mjrgh/PinscapePico/ExpansionBoards/DIY-Friendly/MainBoard/deprecated/README.md

# Older Versions

This folder contains older versions of the board that are no longer
maintained.
