mjrgh/PinscapePico/OpenPinballDevice/Aliasing.png

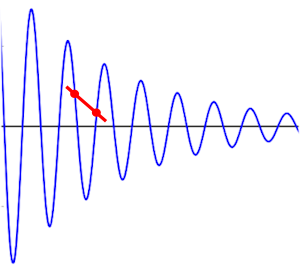
OpenPinballDevice/Aliasing.png
