mjrgh/PinscapePico/OpenPinballDevice/flipper-buttons-2.png

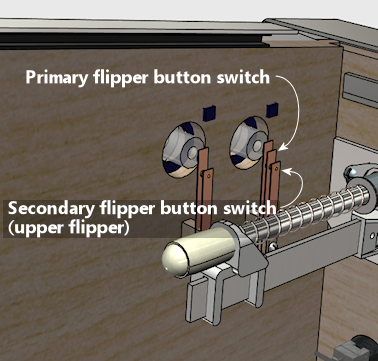
OpenPinballDevice/flipper-buttons-2.png
