mjrgh/PinscapePico/OpenPinballDevice/flipper-buttons.png

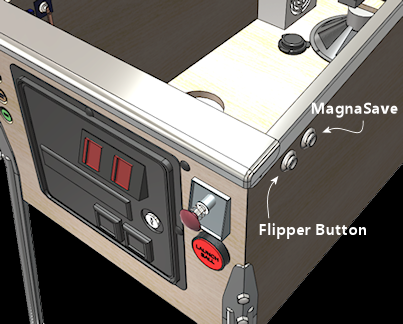
OpenPinballDevice/flipper-buttons.png
