mjrgh/PinscapePico/PWMWorker/DataSheet/high-side-led.png

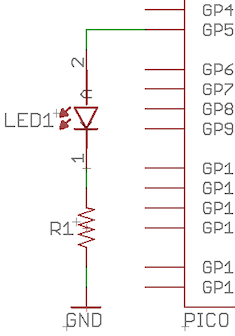
PWMWorker/DataSheet/high-side-led.png
