mjrgh/PinscapePico/PWMWorker/DataSheet/low-side-led.png

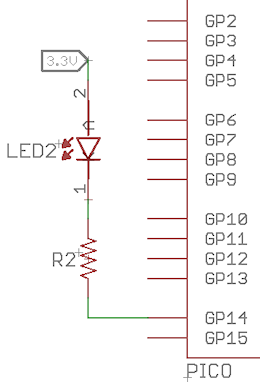
PWMWorker/DataSheet/low-side-led.png
