mjrgh/PinscapePico/PWMWorker/DataSheet/low-side-npn.png

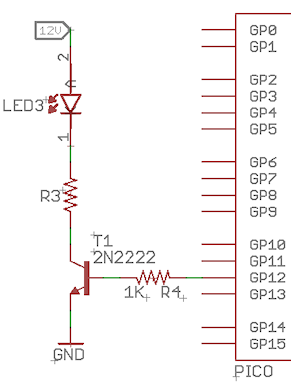
PWMWorker/DataSheet/low-side-npn.png
