mjrgh/PinscapePico/PWMWorker/DataSheet/mosfet-out.png

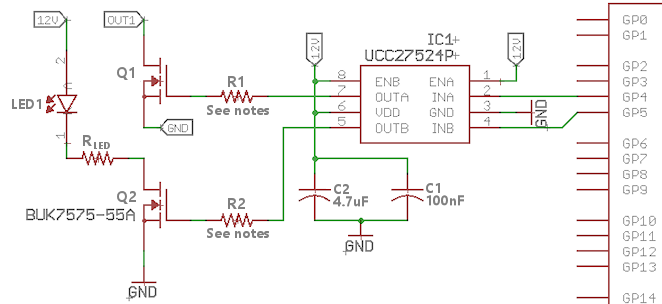
PWMWorker/DataSheet/mosfet-out.png
