mjrgh/PinscapePico/PWMWorker/DataSheet/PinMap.png

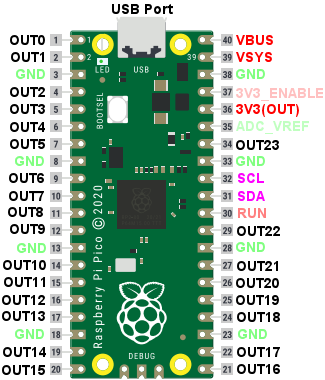
PWMWorker/DataSheet/PinMap.png
