mjrgh/PinscapePico/PWMWorker/DataSheet/PWM-graph.png

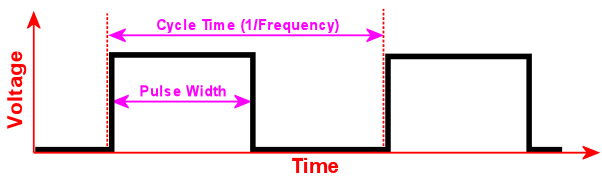
PWMWorker/DataSheet/PWM-graph.png
