mjrgh/PinscapePico/PWMWorker/DataSheet/uln2803.png

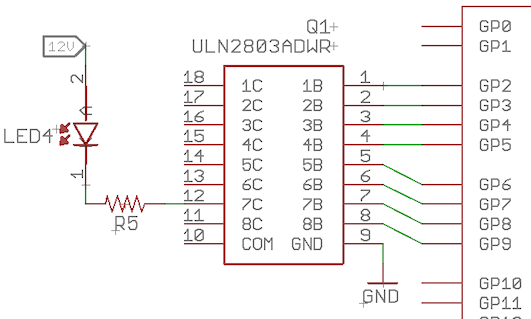
PWMWorker/DataSheet/uln2803.png
