mjrgh/PinscapePico/ScreenShots/ConfigToolButtons.png

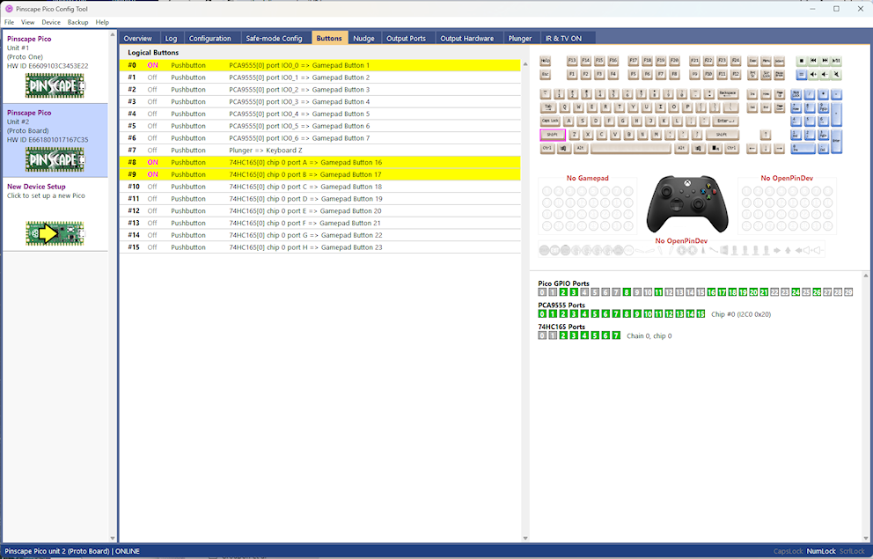
ScreenShots/ConfigToolButtons.png
