mjrgh/PinscapePico/ScreenShots/ConfigToolPlunger-thumb.png

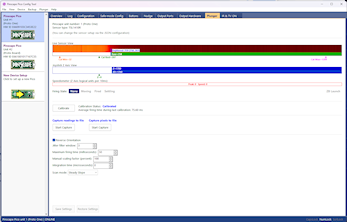
ScreenShots/ConfigToolPlunger-thumb.png
