mjrgh/PinscapePico/ExpansionBoards/KL25Z-Adapter/PinscapePico KL25Z Adapter - PCA9555 vsn.brd

## EAGLE design ExpansionBoards/KL25Z-Adapter/PinscapePico KL25Z Adapter - PCA9555 vsn.brd (2025-02-02)

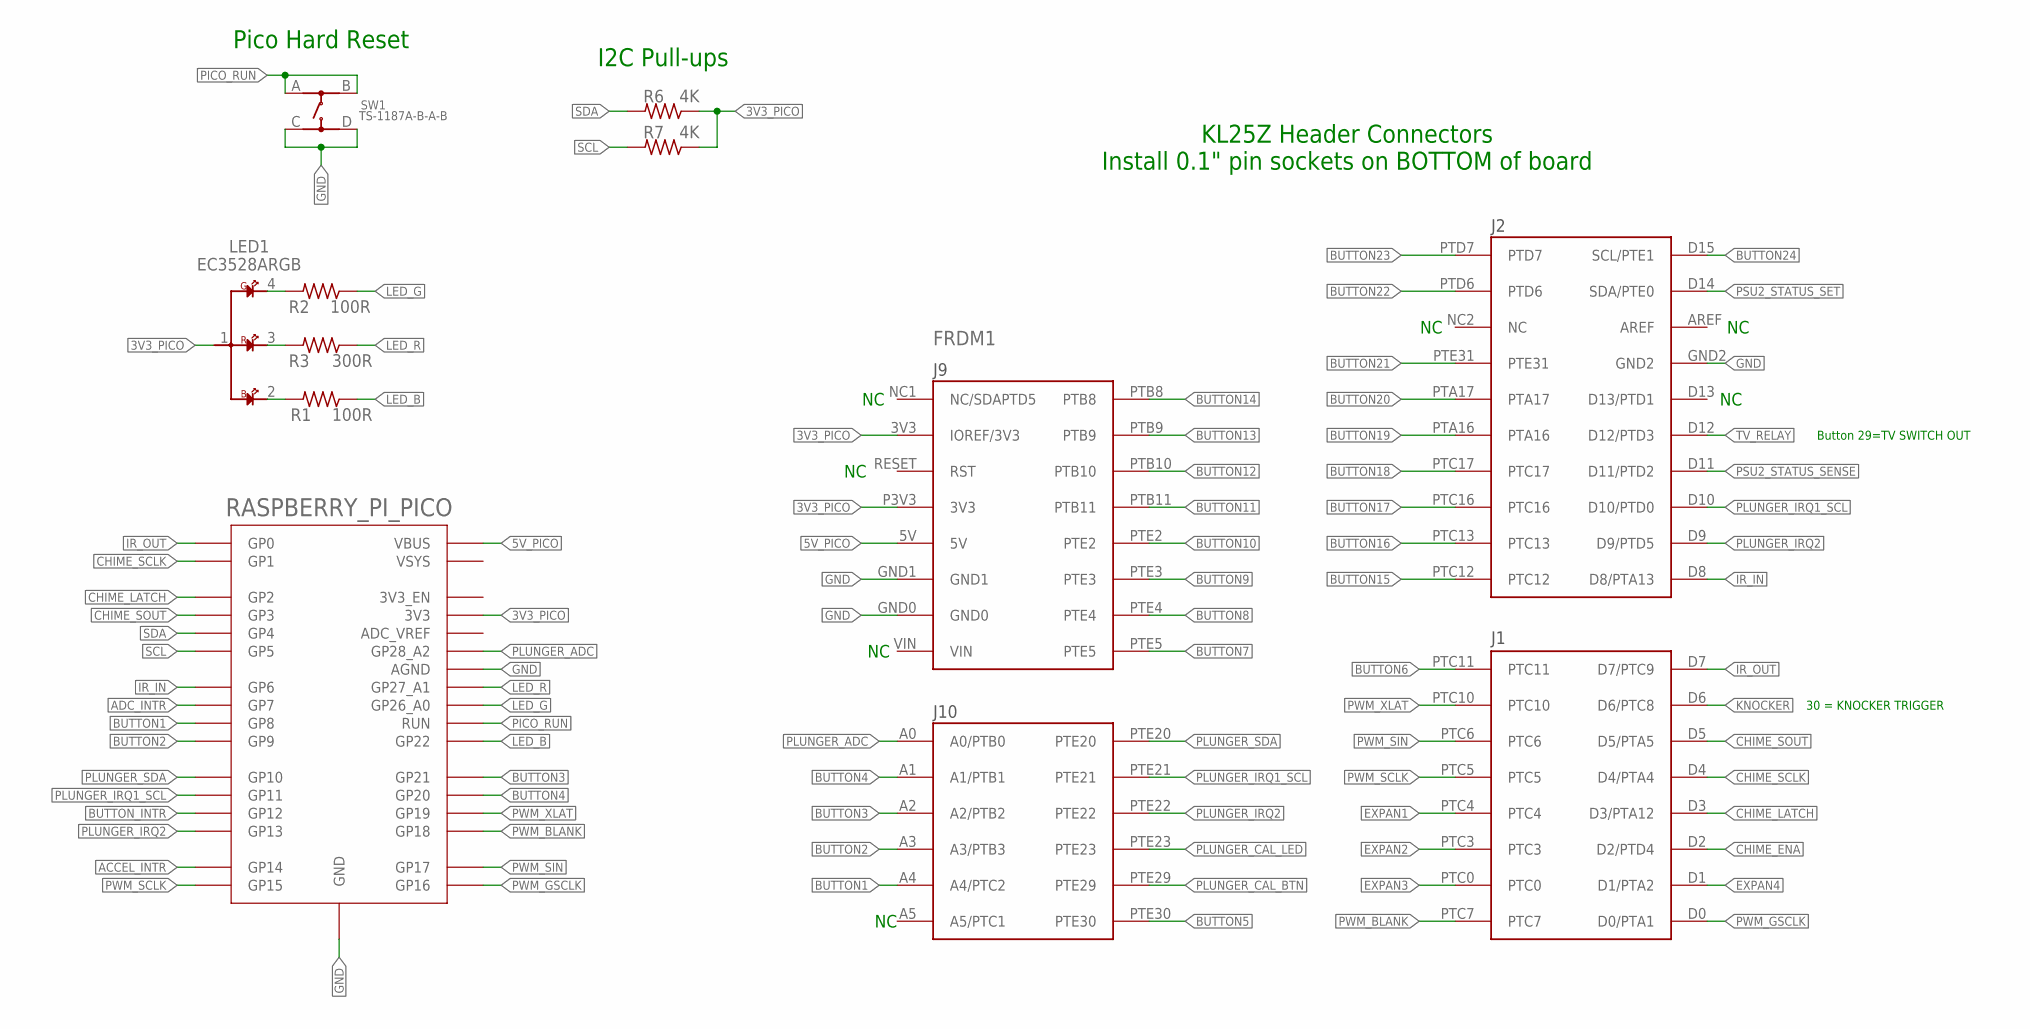
[picture p93: schematic PinscapePico KL25Z Adapter - PCA9555 vsn.sch, sheet 1, Main]

Parts:
FRDM1: KL25Z; FRDM_KL25Z_NORMAL
LED1: EC3528ARGB
R1, R2: 100R; R1206
R3: 300R; R1206
R6, R7: 4K; R1206
RASPBERRY_PI_PICO: RPI_PICO_NO_DEBUG; RPI_PICO_TH_NO_DEBUG
SW1: TS-1187A-B-A-B

Connections:
3V3_PICO: FRDM1.3V3 (IOREF/3V3), FRDM1.P3V3 (3V3), LED1.1, R6.1, R7.1, RASPBERRY_PI_PICO.3V3; also elsewhere on the board
5V_PICO: FRDM1.5V, RASPBERRY_PI_PICO.VBUS
ACCEL_INTR: RASPBERRY_PI_PICO.GP14; also elsewhere on the board
ADC_INTR: RASPBERRY_PI_PICO.GP7; also elsewhere on the board
BUTTON1: FRDM1.A4 (A4/PTC2), RASPBERRY_PI_PICO.GP8
BUTTON2: FRDM1.A3 (A3/PTB3), RASPBERRY_PI_PICO.GP9
BUTTON3: FRDM1.A2 (A2/PTB2), RASPBERRY_PI_PICO.GP21
BUTTON4: FRDM1.A1 (A1/PTB1), RASPBERRY_PI_PICO.GP20
BUTTON5: FRDM1.PTE30; also elsewhere on the board
BUTTON6: FRDM1.PTC11; also elsewhere on the board
BUTTON7: FRDM1.PTE5; also elsewhere on the board
BUTTON8: FRDM1.PTE4; also elsewhere on the board
BUTTON9: FRDM1.PTE3; also elsewhere on the board
BUTTON10: FRDM1.PTE2; also elsewhere on the board
BUTTON11: FRDM1.PTB11; also elsewhere on the board
BUTTON12: FRDM1.PTB10; also elsewhere on the board
BUTTON13: FRDM1.PTB9; also elsewhere on the board
BUTTON14: FRDM1.PTB8; also elsewhere on the board
BUTTON15: FRDM1.PTC12; also elsewhere on the board
BUTTON16: FRDM1.PTC13; also elsewhere on the board
BUTTON17: FRDM1.PTC16; also elsewhere on the board
BUTTON18: FRDM1.PTC17; also elsewhere on the board
BUTTON19: FRDM1.PTA16; also elsewhere on the board
BUTTON20: FRDM1.PTA17; also elsewhere on the board
BUTTON21: FRDM1.PTE31; also elsewhere on the board
BUTTON22: FRDM1.PTD6; also elsewhere on the board
BUTTON23: FRDM1.PTD7; also elsewhere on the board
BUTTON24: FRDM1.D15 (SCL/PTE1); also elsewhere on the board
BUTTON_INTR: RASPBERRY_PI_PICO.GP12; also elsewhere on the board
CHIME_ENA: FRDM1.D2 (D2/PTD4); also elsewhere on the board
CHIME_LATCH: FRDM1.D3 (D3/PTA12), RASPBERRY_PI_PICO.GP2
CHIME_SCLK: FRDM1.D4 (D4/PTA4), RASPBERRY_PI_PICO.GP1
CHIME_SOUT: FRDM1.D5 (D5/PTA5), RASPBERRY_PI_PICO.GP3
EXPAN1: FRDM1.PTC4; also elsewhere on the board
EXPAN2: FRDM1.PTC3; also elsewhere on the board
EXPAN3: FRDM1.PTC0; also elsewhere on the board
EXPAN4: FRDM1.D1 (D1/PTA2); also elsewhere on the board
GND: FRDM1.GND0, FRDM1.GND1, FRDM1.GND2, RASPBERRY_PI_PICO.AGND, RASPBERRY_PI_PICO.GND@1 (GND), RASPBERRY_PI_PICO.GND@2 (GND), RASPBERRY_PI_PICO.GND@3 (GND), RASPBERRY_PI_PICO.GND@4 (GND), RASPBERRY_PI_PICO.GND@6 (GND), RASPBERRY_PI_PICO.GND@7 (GND), RASPBERRY_PI_PICO.GND@8 (GND), SW1.C, SW1.D; also elsewhere on the board
IR_IN: FRDM1.D8 (D8/PTA13), RASPBERRY_PI_PICO.GP6
IR_OUT: FRDM1.D7 (D7/PTC9), RASPBERRY_PI_PICO.GP0
KNOCKER: FRDM1.D6 (D6/PTC8); also elsewhere on the board
LED_B: R1.1, RASPBERRY_PI_PICO.GP22
LED_G: R2.1, RASPBERRY_PI_PICO.GP26_A0
LED_R: R3.1, RASPBERRY_PI_PICO.GP27_A1
unnamed: LED1.3, R3.2
unnamed: LED1.2, R1.2
unnamed: LED1.4, R2.2
PICO_RUN: RASPBERRY_PI_PICO.RUN, SW1.A, SW1.B
PLUNGER_ADC: FRDM1.A0 (A0/PTB0), RASPBERRY_PI_PICO.GP28_A2; also elsewhere on the board
PLUNGER_CAL_BTN: FRDM1.PTE29; also elsewhere on the board
PLUNGER_CAL_LED: FRDM1.PTE23; also elsewhere on the board
PLUNGER_IRQ1_SCL: FRDM1.D10 (D10/PTD0), FRDM1.PTE21, RASPBERRY_PI_PICO.GP11
PLUNGER_IRQ2: FRDM1.D9 (D9/PTD5), FRDM1.PTE22, RASPBERRY_PI_PICO.GP13
PLUNGER_SDA: FRDM1.PTE20, RASPBERRY_PI_PICO.GP10
PSU2_STATUS_SENSE: FRDM1.D11 (D11/PTD2); also elsewhere on the board
PSU2_STATUS_SET: FRDM1.D14 (SDA/PTE0); also elsewhere on the board
PWM_BLANK: FRDM1.PTC7, RASPBERRY_PI_PICO.GP18
PWM_GSCLK: FRDM1.D0 (D0/PTA1), RASPBERRY_PI_PICO.GP16
PWM_SCLK: FRDM1.PTC5, RASPBERRY_PI_PICO.GP15
PWM_SIN: FRDM1.PTC6, RASPBERRY_PI_PICO.GP17
PWM_XLAT: FRDM1.PTC10, RASPBERRY_PI_PICO.GP19
SCL: R7.2, RASPBERRY_PI_PICO.GP5; also elsewhere on the board
SDA: R6.2, RASPBERRY_PI_PICO.GP4; also elsewhere on the board
TV_RELAY: FRDM1.D12 (D12/PTD3); also elsewhere on the board

Notes on the sheet:
Button 29=TV SWITCH OUT
30 = KNOCKER TRIGGER
Pico Hard Reset
I2C Pull-ups
KL25Z Header Connectors Install 0.1" pin sockets on BOTTOM of board

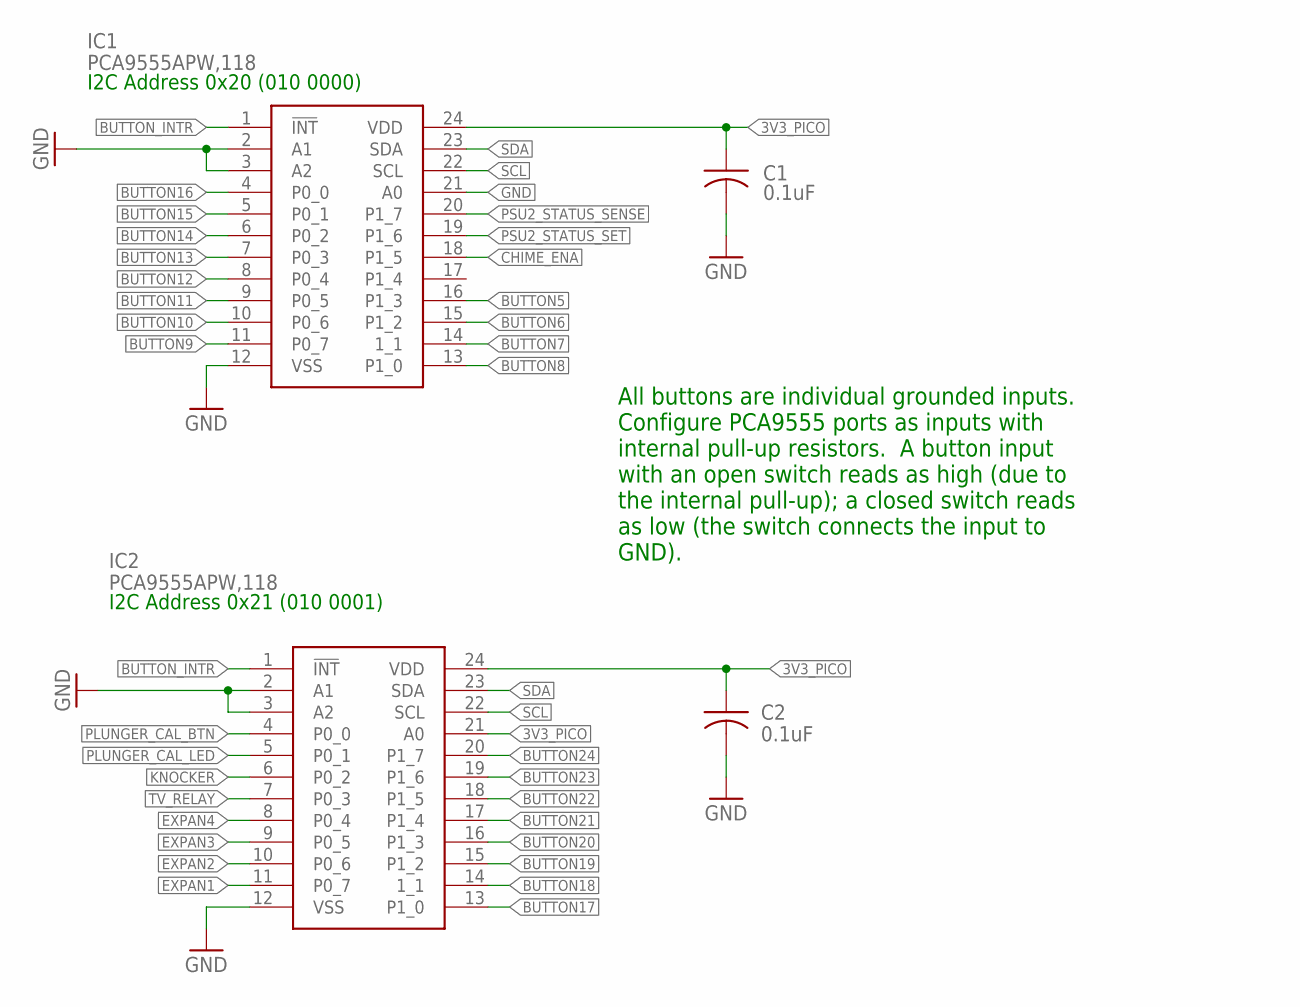
[picture p94: schematic PinscapePico KL25Z Adapter - PCA9555 vsn.sch, sheet 2, Buttons]

Parts:
C1, C2: 0.1uF; C1206
IC1, IC2: PCA9555APW,118; SOP65P640X110-24N

Connections:
3V3_PICO: C1.1, C2.1, IC1.24 (VDD), IC2.21 (A0), IC2.24 (VDD); also elsewhere on the board
BUTTON5: IC1.16 (P1_3); also elsewhere on the board
BUTTON6: IC1.15 (P1_2); also elsewhere on the board
BUTTON7: IC1.14 (1_1); also elsewhere on the board
BUTTON8: IC1.13 (P1_0); also elsewhere on the board
BUTTON9: IC1.11 (P0_7); also elsewhere on the board
BUTTON10: IC1.10 (P0_6); also elsewhere on the board
BUTTON11: IC1.9 (P0_5); also elsewhere on the board
BUTTON12: IC1.8 (P0_4); also elsewhere on the board
BUTTON13: IC1.7 (P0_3); also elsewhere on the board
BUTTON14: IC1.6 (P0_2); also elsewhere on the board
BUTTON15: IC1.5 (P0_1); also elsewhere on the board
BUTTON16: IC1.4 (P0_0); also elsewhere on the board
BUTTON17: IC2.13 (P1_0); also elsewhere on the board
BUTTON18: IC2.14 (1_1); also elsewhere on the board
BUTTON19: IC2.15 (P1_2); also elsewhere on the board
BUTTON20: IC2.16 (P1_3); also elsewhere on the board
BUTTON21: IC2.17 (P1_4); also elsewhere on the board
BUTTON22: IC2.18 (P1_5); also elsewhere on the board
BUTTON23: IC2.19 (P1_6); also elsewhere on the board
BUTTON24: IC2.20 (P1_7); also elsewhere on the board
BUTTON_INTR: IC1.1 (!INT), IC2.1 (!INT); also elsewhere on the board
CHIME_ENA: IC1.18 (P1_5); also elsewhere on the board
EXPAN1: IC2.11 (P0_7); also elsewhere on the board
EXPAN2: IC2.10 (P0_6); also elsewhere on the board
EXPAN3: IC2.9 (P0_5); also elsewhere on the board
EXPAN4: IC2.8 (P0_4); also elsewhere on the board
GND: C1.2, C2.2, IC1.2 (A1), IC1.3 (A2), IC1.12 (VSS), IC1.21 (A0), IC2.2 (A1), IC2.3 (A2), IC2.12 (VSS); also elsewhere on the board
KNOCKER: IC2.6 (P0_2); also elsewhere on the board
PLUNGER_CAL_BTN: IC2.4 (P0_0); also elsewhere on the board
PLUNGER_CAL_LED: IC2.5 (P0_1); also elsewhere on the board
PSU2_STATUS_SENSE: IC1.20 (P1_7); also elsewhere on the board
PSU2_STATUS_SET: IC1.19 (P1_6); also elsewhere on the board
SCL: IC1.22 (SCL), IC2.22 (SCL); also elsewhere on the board
SDA: IC1.23 (SDA), IC2.23 (SDA); also elsewhere on the board
TV_RELAY: IC2.7 (P0_3); also elsewhere on the board

Notes on the sheet:
I2C Address 0x20 (010 0000)
I2C Address 0x21 (010 0001)
All buttons are individual grounded inputs. Configure PCA9555 ports as inputs with internal pull-up resistors. A button input with an open switch reads as high (due to the internal pull-up); a closed switch reads as low (the switch connects the input to GND).

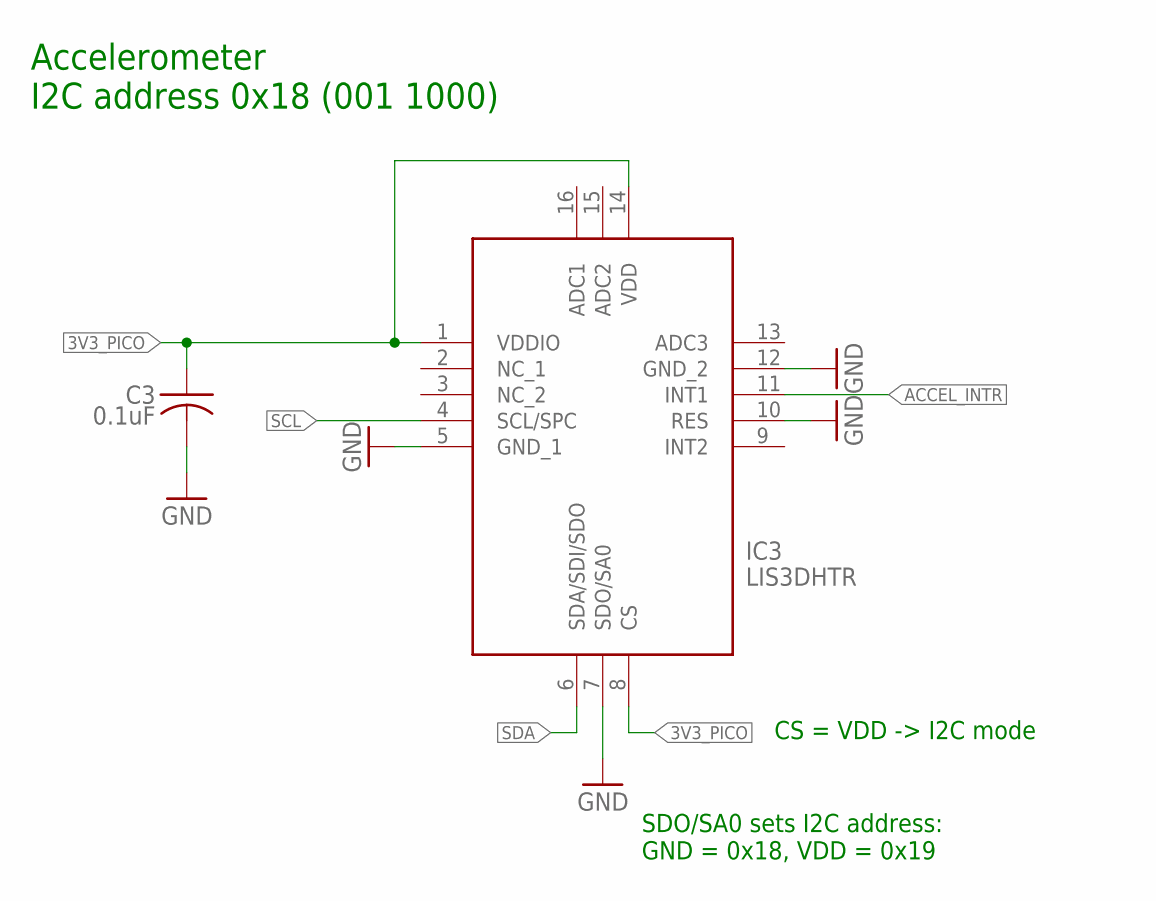
[picture p95: schematic PinscapePico KL25Z Adapter - PCA9555 vsn.sch, sheet 3, Accelerometer]

Parts:
C3: 0.1uF; C1206
IC3: LIS3DHTR

Connections:
3V3_PICO: C3.1, IC3.1 (VDDIO), IC3.8 (CS), IC3.14 (VDD); also elsewhere on the board
ACCEL_INTR: IC3.11 (INT1); also elsewhere on the board
GND: C3.2, IC3.5 (GND_1), IC3.7 (SDO/SA0), IC3.10 (RES), IC3.12 (GND_2); also elsewhere on the board
SCL: IC3.4 (SCL/SPC); also elsewhere on the board
SDA: IC3.6 (SDA/SDI/SDO); also elsewhere on the board

Notes on the sheet:
Accelerometer I2C address 0x18 (001 1000)
SDO/SA0 sets I2C address: GND = 0x18, VDD = 0x19
CS = VDD -> I2C mode

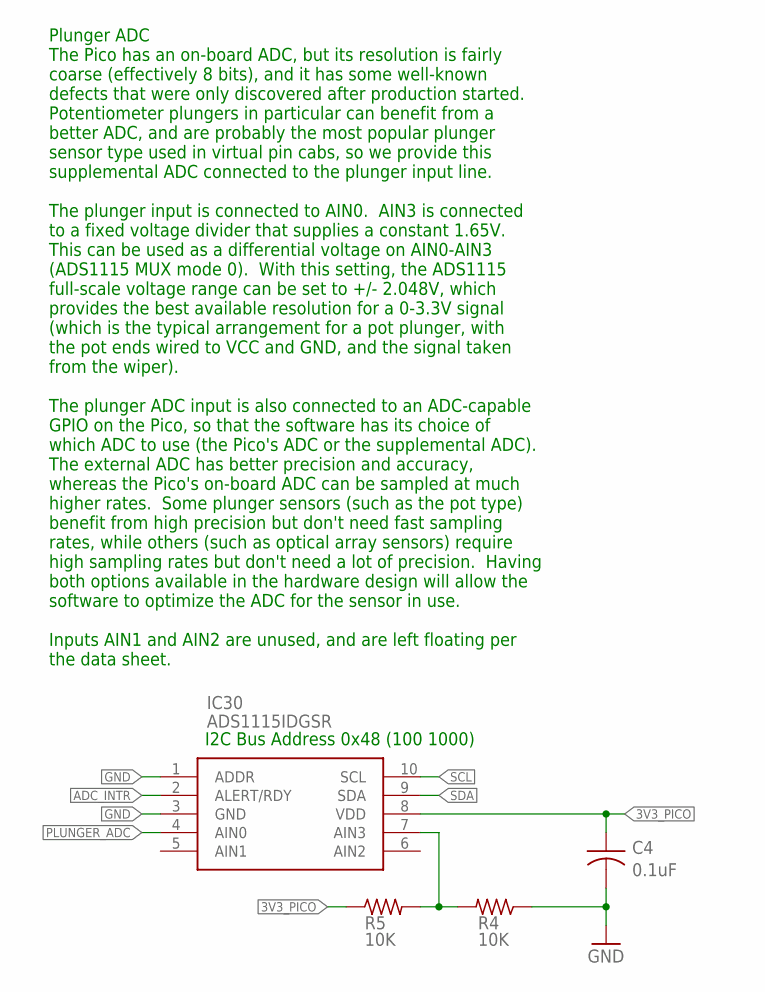
[picture p96: schematic PinscapePico KL25Z Adapter - PCA9555 vsn.sch, sheet 4, ADC]

Parts:
C4: 0.1uF; C1206
IC30: ADS1115IDGSR; SOP50P490X110-10N
R4, R5: 10K; R1206

Connections:
3V3_PICO: C4.1, IC30.8 (VDD), R5.1; also elsewhere on the board
ADC_INTR: IC30.2 (ALERT/RDY); also elsewhere on the board
GND: C4.2, IC30.1 (ADDR), IC30.3 (GND), R4.1; also elsewhere on the board
unnamed: IC30.7 (AIN3), R4.2, R5.2
PLUNGER_ADC: IC30.4 (AIN0); also elsewhere on the board
SCL: IC30.10 (SCL); also elsewhere on the board
SDA: IC30.9 (SDA); also elsewhere on the board

Notes on the sheet:
I2C Bus Address 0x48 (100 1000)
Plunger ADC The Pico has an on-board ADC, but its resolution is fairly coarse (effectively 8 bits), and it has some well-known defects that were only discovered after production started. Potentiometer plungers in particular can benefit from a better ADC, and are probably the most popular plunger se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

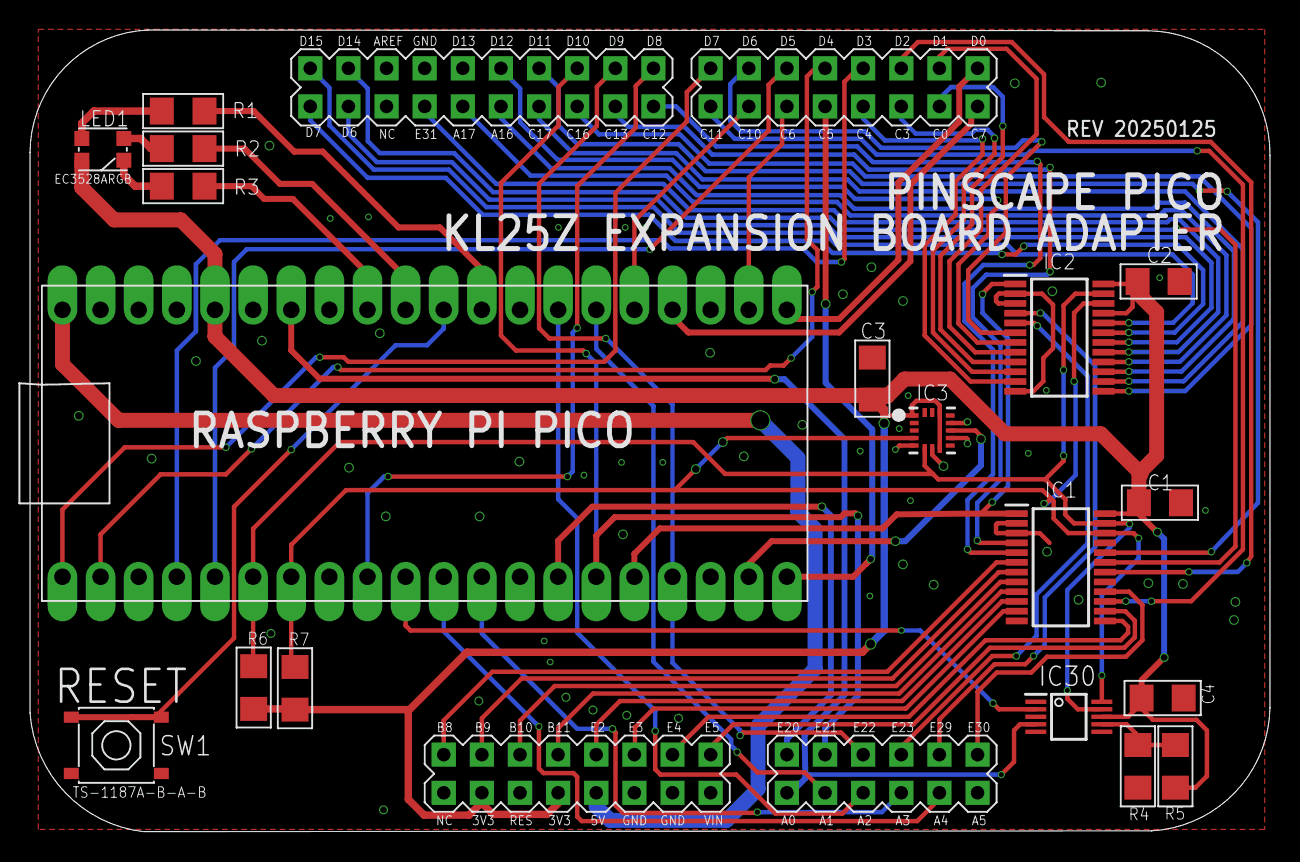
[picture p97: board PinscapePico KL25Z Adapter - PCA9555 vsn.brd from above]

Board: 2 copper layers, 82.6 x 53.4 mm, 19 parts (0 on the bottom side), 65 nets.
