mjrgh/PinscapePico/Firmware/JSONConfigRef.txt

INTRO:
This section provides details on all of Pinscape Pico's JSON configuration
file elements.

For an introduction to the JSON syntax and the overall file layout, refer to
<a href="ConfigFileFormat.htm">Config File Format</a>.

REFERENCE:

pico_adc object optional
  TOC: Peripheral Devices > ADC (Analog-to-digital converters) > Pico On-Board ADC
  TITLE: Pico On-Board ADC (Analog-to-Digital Converter)
  EXAMPLE:
  {
     pico_adc: {
        gpio: [26, 27],
     },
  }

  Sets up the Pico's on-board ADC, which can read from GPIO ports 26-29 and
  from the Pico's internal temperature sensor.  This configuration entry lets
  you use the Pico ADC for input from a potentiometer plunger or a joystick
  input.

  <b>Don't</b> include this entry if you're configuring one of the external
  peripherals that takes over the ADC directly, such as TCD1103 or TSL1410R.
  Those peripherals need special high-speed access to the ADC that requires
  them to take full control of the device, which precludes sharing ADC
  channels with other inputs.

pico_adc.gpio number|[number] required
  Sets the GPIO input port or ports assigned to the Pico ADC.  This can be
  a single port number or a list of port numbers (e.g., [26, 27]).  The
  only ADC-capable ports are 26,  27, 28, 29, and 30.  Port 30 is a
  pseudo-GPIO that's hard-wired to the Pico's internal temperature sensor.
  If you provide a list, the ports must be listed in ascending order.
  The entries in the port list correspond to the ADC channel numbers that
  you can use in joystick axis and plunger assignment entries: "pico_adc"
  is the first channel, assigned to the first GPIO in the list; "pico_adc[1]"
  is the second channel, assigned to the second GPIO in the list; 
  "pico_adc[2]" is the third channel.

buttons [object] optional
  TOC: Button Inputs
  TITLE: Button Inputs
  EXAMPLE:
  {
     // array of button definitions; each entry is an object
     buttons: [
        // button #0 (first array entry)
        { 
            type: "push",
            source: { type: "pca9555", chip: 0, port: 3 },
            action: { type: "key", key: "left shift" },
        },
.
        // button #1 (second array entry)
        { 
            type: "toggle",
            source: { type: "74hc165", chip: 1, port: 7 },
            action: { type: "key", key: "home" },
        },
     ],
  }

  Defines the logical button inputs, which map physical and virtual button
  inputs to actions, such as sending keystrokes to the PC.  Each entry in
  this list is an object that defines one logical button.  Each logical button
  definition has a source, which specifies the physical or virtual input
  that triggers the action, and an action, which specifies what happens when
  you press the source button.  Each logical button can also have a "type",
  which specifies how changes to the physical input are interpreted.  The
  standard type is "pushbutton", which is an ordinary momentary switch that
  carries out its action as long as you're physically pressing the button,
  and stops as soon as you release it.  Other types include "hold" buttons,
  which only carry out their action after being held down for a defined
  interval; "pulse" buttons, which only carry out their action once when
  pushed, rather than continuously while being held down; "toggle" buttons,
  which switch between OFF and ON each time they're pushed, rather than
  staying on only while being held down; and "shift" buttons, which let
  you assign multiple meanings to other buttons, analogous to the keys
  like SHIFT, CTRL, and ALT on a PC keyboard.

  Buttons are defined using two main abstractions:
  <ul>
    <li><b>Sources,</b> which define the physical input that controls
    the button.  This is usually a literal button, such as a flipper
    button or Start button, but it can also be a physical input that's
    not quite a plain switch, such as a command code on the IR receiver,
    or a the plunger or accelerometer readings crossing a threshold.
    <li><b>Actions,</b> which define what happens when the button is
    activated.  For most buttons, this will be a simple input to the
    PC via one of the virtual HID devices, such as a simulated press on
    a keyboard key or a joystick button.  But, like sources, actions
    can have other effects as well, such as sending an IR command or
    executing a series of steps (a "macro").
  </ul>

  Each <tt>buttons[]</tt> entry's main job is to connect a source and
  an action.  When the source records an activation (pressing the
  physical button, receiving the IR command, crossing an accelerometer
  threshold), the action is carried out.

  The same source can be used more than once (that is, in 
  more than one <tt>buttons[]</tt> array entry).  This lets you map
  a single physical input to multiple actions to be carried out, such
  as sending both a keyboard key press and a joystick button press to
  the PC whenever the button is pressed.  Macros can also be used to
  carry out multiple effects for each button press, with the additional
  feature that macros can control the timing of the sub-actions.

buttons[].name string optional
  Assigns the button a name, which you can use to refer to the button
  elsewhere in the configuration, such as in a computed <a href="#outputs.source">output source</a>
  (via the <tt>button()</tt> source type).

buttons[].source object required
  Specifies the physical device port or data source that serves as the
  input for the logical button state.  For a physical button, this is a
  hardware port connected to the button switch, such as a Pico GPIO port
  or a shift register input port.  Buttons can also take their input from
  software sources, such as the plunger and nudge subsystems, or the IR
  remote control receiver.

buttons[].source.type string{"gpio" "bootsel" "pca9555" "74hc165" "nudge" "IR" "plunger" "zblaunch" "clock" "output" "adc"} required
  The source type.  See the source types below for more details.

buttons[].source.type="output"
  Sets the button to track the state of a logical output port (a DOF port).
  The button source acts like it's ON when the output port is within (or outside of)
  a specified value range.  This lets you create buttons that are controlled by
  software on the PC, or by locally computed output ports.

buttons[].source.type="output".port number|string required
  Identifies the logical output port used as the source of the button's ON/OFF state.
  This is either a number giving the logical output port number, or a string giving
  the output port name.  If this is a number, it gives the DOF port number, which is the 
  same as the location in the config file <a href="#outputs"><tt>outputs</tt></a> array, 
  where port 1 is the first element in the array, 2 is the second element, etc.
  If this is a string, it's matched against the <a href="#outputs.name"><tt>name</tt></a>
  properties of the output ports to identify the port.

buttons[].source.type="output".range object optional
  Specifies the value range on the output port that triggers the button's ON state.
  By default, the range is <tt>{min: 1, max: 255, inside: true}</tt>, which means
  that the button is ON when the output port is at any non-zero value (since port
  levels are always in the range 0 to 255).

buttons[].source.type="output".range.min number optional
  Sets the low end of the value range on the output port that triggers the button.
  The range is inclusive of the minimum and maximum, so a value is within the range
  if it's greater than or equal to <tt>min</tt> <b>and</b> less than or equal to
  <tt>max</tt>.  By default, <tt>min</tt> is 1.

buttons[].source.type="output".range.max number optional
  Sets the high end of the value range on the output port that triggers the button.
  The range is inclusive of the minimum and maximum, so a value is within the range
  if it's greater than or equal to <tt>min</tt> <b>and</b> less than or equal to
  <tt>max</tt>.  By default, <tt>max</tt> is 255, which is the highest level value
  that an output port can be set to.

buttons[].source.type="output".range.inside bool optional
  Sets the inside/outside test for the range.  This is <tt>true</tt> by default,
  which means that the button is ON when the output port's value is within
  the range, i..e, <tt>min</tt> &le; <i>port_value</i> &le; <tt>max</tt>.
  If this is <tt>false</tt>, the button is ON when the output port's value
  is outside of the range - less than <tt>min</tt> or greater than <tt>max</tt>.

buttons[].source.type="gpio"
  Defines the button as a GPIO input, wired to a physical switch through
  a Pico GPIO port.

buttons[].source.type="gpio".gp number required
  Sets the GPIO port for the button input.

buttons[].source.type="gpio".pull bool optional
  If true, the GPIO port will be configured with an internal pull-up
  or pull-down resistor, as appropriate for the active="high" or "low"
  setting for the button.  True by default.  A pull resistor is
  generally required for ordinary buttons and switches, but you should
  disable the internal one if you provide your own external pull resistor,
  or if you're attaching some kind of device that drives the line high
  and low on its own.  Some types of powered coin acceptor mechanisms
  actively drive the line high and low, for example.

buttons[].source.type="gpio".lowPassFilterRiseTime number optional
  Sets the debouncing low-pass filter time for rising edges, in microseconds.
  This is the minimum amount of time that the GPIO port must remain in the HIGH
  state after a "rising edge" - a LOW-to-HIGH voltage transition on the GPIO port -
  before Pinscape will recognize the new HIGH state.  This is designed to filter
  out random electrical noise on the input, by requiring that the new HIGH level
  remain in effect continuously for a minimum amount of time before it's treated
  as legitimate.

  The RISE time applies to physical LOW-to-HIGH voltage transitions on the port,
  regardless of the active-high/low setting on the port.

  Unlike the <tt>debounceTimeOn/Off</tt> "hold" times, the low-pass filter
  adds latency to input recognition, since the software won't recognize a
  physical button press until the low-pass filter time elapses.  This value
  should therefore be kept as small as possible.  The default is 0, which
  doesn't apply any low-pass filtering at all.  For many switches, the
  latency-free <tt>debounceTimeOn/Off</tt> settings are all you need to
  eliminate switch bounce artifacts, but some switches have enough intrinsic
  noise that low-pass filtering is also required.

buttons[].source.type="gpio".lowPassFilterFallTime number optional
  Sets the debouncing low-pass filter time for falling edges, in microseconds.
  This is the minimum amount of time that the GPIO port must remain in the LOW
  state after a "falling edge" - a HIGH-to-LOW voltage transition on the GPIO port -
  before Pinscape will recognize the new LOW state.  This is designed to filter
  out random electrical noise on the input, by requiring that the new LOW level
  remain in effect continuously for a minimum amount of time before it's treated
  as legitimate.

  The FALL time applies to physical HIGH-to-LOW voltage transitions on the port,
  regardless of the active-high/low setting on the port.

  Unlike the <tt>debounceTimeOn/Off</tt> "hold" times, the low-pass filter
  adds latency to input recognition, since the software won't recognize a
  physical button press until the low-pass filter time elapses.  This value
  should therefore be kept as small as possible.  The default is 0, which
  doesn't apply any low-pass filtering at all.  For many switches, the
  latency-free <tt>debounceTimeOn/Off</tt> settings are all you need to
  eliminate switch bounce artifacts, but some switches have enough intrinsic
  noise that low-pass filtering is also required.

buttons[].source.type="gpio".debounceTimeOn number optional
  Sets the debouncing ON hold time for the GPIO input, in microseconds.
  Most physical switches "bounce" when switching between ON and OFF
  states, which means that the voltage level on the switch oscillates
  very rapidly for a brief time after the moment of contact.  The
  brief instability in the signal can cause odd behavior in some
  host software reading the switch state; for example, if a button
  is mapped to keyboard input, the bounce effect might cause the
  key input to be repeated several times for a single button press.
  Debouncing refers to any sort of filtering that suppresses the
  oscillations after an on/off transition.  Pinscape Pico debounces
  inputs by ignoring any <i>further</i> on/off changes for a brief time 
  after each valid on/off change.  This parameter sets the duration of
  that suppression time after an ON transition (from OFF to ON). 
  The default value is 1500 microseconds (1.5 milliseconds), which
  is long enough to suppress bounce in typical microswitches.  If 
  you experience any spurious input from a button, especially
  repeated inputs for a single button press, you can try increasing
  the time.

buttons[].source.type="gpio".debounceTimeOff number optional
  Sets the debouncing "OFF" time for the switch input, in microseconds.
  This is the counterpart of <tt>debounceTimeOn</tt>, for when the
  switch transitions to OFF (releasing the button).  Switches typically
  settle into the OFF state more quickly than into the ON state, so this
  can usually be set to a shorter value than the ON time.  The default
  is 1000 microseconds (1 millisecond).

buttons[].source.type="gpio".enableLogging bool optional
  If true, the port will be configured to enable hardware interrupts
  on logic-level changes on the port's voltage input, and the interrupt
  handler will record the time of each transition in an internal log.
  Software on the PC host can retrieve the event log and use it to
  analyze the latency (elapsed time) between physical button presses
  and the corresponding HID reports to the PC.  The Pico can service
  hardware interrupts with very low latency, on the order of 200
  nanoseconds, and records the event time with microsecond precision,
  so the host can measure HID latencies with very good precision.

  This option is only intended for use with performance measuring
  tools on the PC.  It doesn't do anything useful in ordinary operation
  with a pinball simulator, and it adds a small amount of overhead on
  the Pico side to service the interrupts and reserve memory for the
  log buffer, so it's best to disable it when not running performance
  tests.  

buttons[].source.type="bootsel"
  Sets the button's input source as the BOOTSEL button - the little 
  button on top of the Pico that's normally used to put the Pico into
  its Boot Loader mode during a reset.  This button can be used as an
  ordinary input because its special Boot Loader function only takes
  effect while the Pico is resetting.

buttons[].source.type="pca9555"
  Connects the button to an input port on a PCA9555 chip.  The PCA9555
  is a GPIO expander chip that adds 16 digital (on/off) ports that can
  be used much like the Pico's own GPIO ports, including as button 
  inputs.  You can attach several of these chips to the Pico to add
  a large number of button parts.

buttons[].source.type="pca9555".chip number required
  The PCA9555 chip number, as an index in the "pca9555:" array in
  the JSON configuration file.  The first chip listed in the array is
  number 0, the second chip is number 1, etc.

buttons[].source.type="pca9555".port string required
  The name of the port on the PCA9555 chip, as a string giving the
  pin label as in the data sheet.  The input pins are arranged in two
  banks, "0" and "1", each with ports 0 to 7.  The NXP data sheet
  uses the notation "IO1_5" (that's the letter I and the letter O,
  then bank number 1, underscore, port number 5).  The TI data
  sheet reduces this to just "15" for Bank 1, Port 5.  You can use
  either notation in the JSON file.

buttons[].source.type="74hc165"
  Sets the button's input source to a port on a 74HC165 chip.  The
  74HC165 is an input shift-register chip with 8 digital on/off input
  ports, which can be used as button inputs.  Multiple 74HC165 chips can
  be daisy-chained, letting you add more input ports in groups of 8 as
  needed.

buttons[].source.type="74hc165".chain number optional
  The daisy chain number.  This is an index into the "74hc165:" array
  in the JSON configuration file, selecting which daisy chain this button
  is associated with.  If you only have a single chain (which is almost
  always the case - it's rare to configure more than one), you can omit
  this, and the system will know you mean to use the one-and-only.

buttons[].source.type="74hc165".chip number optional
  The chip number on the daisy chain.  The first chip on the chain (the
  one attached directly to the Pico) is number 0, the second is number 1,
  and so on.  If you include this, then you only have to give the port
  number relative to the chip; if you omit it, the port number is
  specified in terms of the whole chain.

buttons[].source.type="74hc165".port string|number required
  The input pin on the selected daisy chain.  If you specify the "chip"
  property to select a chip on the chain, the port should be specified
  as simply "A" to "H", corresponding to the pin labels used in the 
  chip's data sheet.  To make things more compact, you can skip the
  "chip" property and instead include it here, as in "0A" for pin A
  on the first chip on the chain, or "1H" for pin H on the second chip.

  You can also use the NXP data sheet notation, where the ports are
  labeled D0 through D7 (instead of A through H, as the TI data sheet
  would have it).  The chip number prefix works here, too:  "1D3" for
  pin D3 on chip index 1 (the second chip on the daisy chain).

  Alternatively, you can specify this as a pin number, 0-7 on each
  chip corresponding to pin A-H.  If you omit the chip number, you
  can specify ports 0-7 for the first chip on the chain, 8-15 for
  the second chip, 16-23 for the third, and so on.  I think the
  string notation is clearer, though.

buttons[].source.type="74hc165".lowPassFilterRiseTime number optional
  Sets the debouncing low-pass filter time for rising edges, in microseconds.
  This is the minimum amount of time that the 74HC165 port must remain in the HIGH
  state after a "rising edge" - a LOW-to-HIGH voltage transition on the port -
  before Pinscape will recognize the new HIGH state.  This is designed to filter
  out random electrical noise on the input, by requiring that the new HIGH level
  remain in effect continuously for a minimum amount of time before it's treated
  as legitimate.

  The RISE time applies to physical LOW-to-HIGH voltage transitions on the port,
  regardless of the active-high/low setting on the port.

  Unlike the <tt>debounceTimeOn/Off</tt> "hold" times, the low-pass filter
  adds latency to input recognition, since the software won't recognize a
  physical button press until the low-pass filter time elapses.  This value
  should therefore be kept as small as possible.  The default is 0, which
  doesn't apply any low-pass filtering at all.  For many switches, the
  latency-free <tt>debounceTimeOn/Off</tt> settings are all you need to
  eliminate switch bounce artifacts, but some switches have enough intrinsic
  noise that low-pass filtering is also required.

buttons[].source.type="74hc165".lowPassFilterFallTime number optional
  Sets the debouncing low-pass filter time for falling edges, in microseconds.
  This is the minimum amount of time that the 74HC165 port must remain in the LOW
  state after a "falling edge" - a HIGH-to-LOW voltage transition on the port -
  before Pinscape will recognize the new LOW state.  This is designed to filter
  out random electrical noise on the input, by requiring that the new LOW level
  remain in effect continuously for a minimum amount of time before it's treated
  as legitimate.

  The FALL time applies to physical HIGH-to-LOW voltage transitions on the port,
  regardless of the active-high/low setting on the port.

  Unlike the <tt>debounceTimeOn/Off</tt> "hold" times, the low-pass filter
  adds latency to input recognition, since the software won't recognize a
  physical button press until the low-pass filter time elapses.  This value
  should therefore be kept as small as possible.  The default is 0, which
  doesn't apply any low-pass filtering at all.  For many switches, the
  latency-free <tt>debounceTimeOn/Off</tt> settings are all you need to
  eliminate switch bounce artifacts, but some switches have enough intrinsic
  noise that low-pass filtering is also required.

buttons[].source.type="74hc165".debounceTimeOn number optional
  Sets the debouncing "ON" time for the switch input, in microseconds.
  Most physical switches "bounce" when switching between ON and OFF
  states, which means that the voltage level on the switch oscillates
  very rapidly for a brief time after the moment of contact.  The
  brief instability in the signal can cause odd behavior in some
  host software reading the switch state; for example, if a button
  is mapped to keyboard input, the bounce effect might cause the
  key input to be repeated several times for a single button press.
  Debouncing refers to any sort of filtering that suppresses the
  oscillations after an on/off transition.  Pinscape Pico debounces
  inputs by ignoring any <i>further</i> on/off changes for a brief time 
  after each valid on/off change.  This parameter sets the duration of
  that suppression time after an ON transition (from OFF to ON, when
  the button is pressed).  The default value is 1500 microseconds 
  (1.5 millisecond), which is long enough to suppress bounce in
  typical microswitches.  If you experience any spurious input
  from a button, especially repeated inputs for a single button
  press, you can try increasing this.  Longer values have the
  disadvantage that they limit the rate at which intentional
  fast taps can be processed.

buttons[].source.type="74hc165".debounceTimeOff number optional
  Sets the debouncing "OFF" time for the switch input, in microseconds.
  This is the counterpart of <tt>debounceTimeOn</tt>, for when the
  switch transitions to OFF (releasing the button).  Switches typically
  settle into the OFF state more quickly than into the ON state, so this
  can usually be set to a shorter value than the ON time.  The default
  is 1000 microseconds (1 millisecond).

buttons[].source.type="nudge"
  This sets up a virtual button that's triggered by an accelerometer
  event.  You can set the force and direction required to trigger the
  button.

buttons[].source.type="nudge".axis string required
  Sets the source axis for the event: "x", "y", or "z".

buttons[].source.type="nudge".direction string optional
  Sets the direction of the nudge on the selected axis: "+" for the positive
  direction only, "-" for the negative direction, "+-" for either direction.

buttons[].source.type="nudge".threshold number required
  The minimum reading on the nudge axis to trigger the event, 0 to 32767.
  
buttons[].source.type="nudge".onTime number optional
  The amount of time to pulse the imaginary button, in milliseconds
  (1000 milliseconds equals one second).  When the nudge axis reading goes
  over the threshold, the button reads as pressed for this interval.

buttons[].source.type="nudge".resetTime number optional
  The reset time for the nudge event, in milliseconds (1000 milliseconds
  equals one second).  Each time the button is triggered, it performs its
  action, and then ignores the nudge input for this amount of time.  This
  prevents the button from getting triggered repeatedly during a strong
  jolt to the cabinet.

buttons[].source.type="IR"
  Sets up the button as an IR command receiver.  The button will trigger
  its action when the specified IR command is receive on the IR remote
  control sensor.  An IR receiver must be attached and configured for
  this to work, obviously.

buttons[].source.type="IR".code string required
  The IR command code that triggers the button.  This is a string in the
  Pinscape universal IR code format.  The easiest way to determine the
  code that goes with a particular button is to use the Pinscape Config Tool's
  IR & TV ON tester window, which shows command codes for commands
  received while the window is open.  Just copy a command code from
  that window into the "code" property.

buttons[].source.type="IR".latchTime number optional
  The "latching" time for the command, in milliseconds (1000 milliseconds
  equals one second).  The button stays activated for this amount of time
  each time the code is received.  This is designed to make the logical
  button's action on the PC stay on continuously when you're holding down the
  button on the remote.  IR remotes don't have a direct way to tell the receiver
  that the button is being held down; instead, they transmit the same code
  repeatedly at short intervals.  So if you hold down the button on the
  remote, Pinscape will see a series of repeated codes.  The latchTime
  tells Pinscape to keep holding the logical button ON for a little while
  after each code, to see if a repeat of the code is forthcoming.  If you
  make this interval long enough that the codes overlap, the logical button
  will remain on continuously as long as you're holding down the remote
  button.  That smooths out the "pulse train" from the IR remote and turns
  it into what looks like a push-and-hold on the logical button.

buttons[].source.type="IR".firstRepeatDelay number optional
  This is a sort of book-end to the latchTime property.  This sets the
  amount of time to wait after the command is received before the ON time
  for the logical button will be extended with repeats of the code.  This
  is meant to help distinguish short taps on the button from long presses.
  The reason this is needed is that most IR remote controls start transmitting
  repeats very quickly, so quickly that a quick tap on a button can often
  send two or three repeats of the code.  With the latchTime property extending
  the ON time after each code, the repeats can make a short tap on the physical
  IR remote button turn into a much longer hold on the logical button, which
  might not produce the right effect on the PC.  The firstRepeatDelay is
  intended to help with that by ignoring initial repeats for a short time.

buttons[].source.type="plunger"
  Sets up the logical button to trigger its action when the plunger
  position is inside or outside of a specified range.

buttons[].source.type="plunger".range object optional
  Sets the plunger range that triggers the button.

buttons[].source.type="plunger".range.min number optional
  The low end of the trigger range, -32768 to +32767.

buttons[].source.type="plunger".range.max number optional
  The high end of the trigger range, -32768 to +32767.

buttons[].source.type="plunger".range.inside bool optional
  Set this to true (which is also the default if you don't specify it)
  to trigger the button when the plunger position is inside the min-max
  range - that is, when the position is greater than the minimum and
  less than the maximum.  Set it to false to trigger when the position
  is outside of the min-max range.

buttons[].source.type="plunger".fire bool optional
  Set this to true to trigger the button whenever a firing event on
  the plunger is detected.  A firing event occurs when the user pulls
  back the plunger and releases it, or, equivalently, just moves it
  forward fast enough to mimic the same motion.  If this is true
  and a range is also specified, the button will trigger on either
  condition - that is, on a firing event OR whenever the position is
  inside/outside the range.

buttons[].source.type="plunger".fireOnTime number optional
  Sets the "on" time after a firing event occurs, in milliseconds (1000
  milliseconds equals one second).  The button reads as pressed for this
  long after a firing event.  When the button action is mapped to a keyboard
  key press or gamepad button press, it's usually necessary to hold the
  button press for a brief time, on the order of 10 to 20 milliseconds,
  to ensure that the PC detects the event.

buttons[].source.type="zblaunch"
  Sets up the logical button to trigger whenever a ZB Launch event occurs.
  A ZB Launch event occurs whenever a "firing" event occurs (that is, the
  user pulls back the plunger and releases it), or when the user presses
  the plunger forward onto the barrel spring as though pressing a button.

buttons[].source.type="zblaunch".modal bool optional
  If this is set to true, which is the default, the button only triggers
  when ZB Launch Mode is in effect, as set through the DOF port assigned
  as the ZB Launch indicator.  Set this to false to trigger the button
  on a ZB Launch gesture even when the mode isn't in effect.

buttons[].source.type="adc"
  Sets up the logical button to trigger whenever an ADC (analog to
  digital converter) reading is either above or below the configured
  threshold value.

  This is useful for connecting input controls that are based on
  variable resistors (potentiometers) instead of simple on/off switches,
  such as joysticks, dials, and slider controls.  You can connect this
  kind of input control through an ADC - either the Pico's built-in
  ADC, or an external ADC chip - and then treat it as a simple on/off
  button using this logical button source type.  Physically, the device
  will vary the voltage fed into the ADC as you move the control along
  its range.  Pinscape will convert this into an on/off button action
  by treating voltage readings on one side of the selected voltage
  threshold as ON, and readings on the other side as OFF.

buttons[].source.type="adc".adc string required
  The name of the ADC device to use as the input for the button.
  If you configure an ADC device with multiple channels, and you want
  to use one of those for a potentiometer plunger input, you'll have
  to set this to specify which channel to use.  For the Pico on-board
  ADC, set this to "pico_adc" to use the first configured channel for
  the plunger, "pico_adc[1]" to use the second channel, "pico_adc[2]"
  for the third channel, and so on.

buttons[].source.type="adc".above bool optional
  If this is set to true, which is the default, the button reads as ON
  when the ADC reading is higher than the <tt>threshold</tt> value.  When
  set to false, the button reads as ON when the analog reading is lower
  than the <tt>threshold</tt> value.

buttons[].source.type="adc".threshold number optional
  Sets the ADC reading at which the button will trigger, using the
  "normalized" range of 0 to 65535.  The Pinscape software internally
  maps every device's native range to the same 0..65535 scale, where 0
  corresponds the minimum voltage that the device can register, and
  65535 corresponds to the maximum voltage.  If this value is
  omitted, the default is 32767, which represents the halfway point
  on the ADC's voltage range.

  If <tt>above</tt> is true, which is the default, the button will
  read as ON (pressed) whenever the ADC reading is higher than the
  <tt>threshold</tt> value.  Otherwise, the button is ON when the
  ADC reading is below the threshold value.

buttons[].source.active string{high low} optional
  "high" for a button whose port reads logic "1" when pressed, "low" for
  a port that reads logic "0".  For physical inputs like GPIO ports and
  shift register inputs, a port is active-high if the switch connects the
  port to 3.3V when the button is pressed, and active-low if it connects
  to GND when pressed.  The standard wiring is "active low", where one
  terminal of the switch is connected to the input port, and the other
  terminal is connected to GND.  If this property is omitted, the default
  is active-low.

buttons[].remoteWake bool optional
  Marks the button as a USB wake-up button.  If this is true, pressing
  the button while the PC is in sleep mode will send a USB wake-up signal
  to the PC.  (The PC has to be configured to obey wake-up signals, which
  is usually the default on Windows PCs, but it might require modifying
  settings in your Windows power preferences and possibly the PC's BIOS.)

buttons[].action object required
  This is an object that specifies the action that's triggered when the
  logical button is activated by its input source.

buttons[].action.type string{table} required
  This specifies which type of action to take when the button is activated.
  <table>
    <tr><th>Type</th><th>Description</th></tr>
    <tr><td>"key"</td><td>Keyboard key press</td></tr>
    <tr><td>"media"</td><td>Media controller key press</td></tr>
    <tr><td>"gamepad"</td><td>Gamepad button press</td></tr>
    <tr><td>"xInput"</td><td>XBox controller button press</td></tr>
    <tr><td>"openPinDev"</td><td>Open Pinball Device button press</td></tr>
    <tr><td>"reset"</td><td>Reset the Pico</td></tr>
    <tr><td>"nightmode"</td><td>Toggle Night Mode</td></tr>
    <tr><td>"plungercal"</td><td>Start plunger calibration</td></tr>
    <tr><td>"IR"</td><td>Send an IR command on the IR transmitter</td></tr>
    <tr><td>"macro"</td><td>Execute a macro</td></tr>
    <tr><td>"none"</td><td>Do nothing</td></tr>
  </table>

buttons[].action.type="openPinDev"
  This sets up the button to send input through the Open Pinball Device
  interface.

  To use this type of button mapping, the Open Pinball Device HID
  interface must be enabled via the <a href="#openPinballDevice.enable">openPinballDevice.enable</a>
  property.

buttons[].action.type="openPinDev".button number|string required
  Sets the Open Pinball Device virtual button to activate when this
  physical button is pressed.

  The Open Pinball Device interface provides two kinds of buttons:
  a set of 32 "generic" numbered buttons, identified simply as button
  numbers 1 through 32; and a collection of pre-defined, named "pinball" buttons,
  with specific assigned functions that map to the standard functions that
  most of the PC pinball simulators use, such as "Start Game", "Launch Ball",
  "Left Flipper", and so on.   The generic numbered buttons and the name pinball 
  buttons are completely independent of one another, so this gives you a total
  of 59 assignable buttons:  32 generic numbered buttons plus the 27 named
  buttons.

  To assign an action to a generic button, set <tt>button</tt> to 
  a number from 1 to 32.  These buttons are comparable to gamepad buttons,
  in that they don't have any pre-assigned meanings; they're just generic
  buttons that you can assign to a selected function in each PC program
  you're using.  You have to go into each program's setup options or
  configuration file to map the numbered buttons to in-program functions.
  In Visual Pinball, for example, the generic Open Pinball Device buttons
  are treated exactly like joystick buttons, so you assign the VP function 
  of generic button #1 by going into VP's Keys dialog and assigning one
  of the command keys to Joystick Button #1.

  The pinball buttons are a separate set of virtual buttons that are 
  pre-assigned to the common functions found in almost all of the pinball
  simulator programs.  The nice thing about the pinball buttons is that
  the compatible simulators have built-in mappings for these, so you don't
  have to manually configure them in each simulator.  Just assign a physical
  button to "start", and it'll automatically act as the Start button in 
  every compatible simulator.  To set up a pinball button action, use one
  of the strings shown below for the <tt>button</tt> value.
  <table>
    <tr><th>Button name</th><th>Description</th></tr>
    <tr><td>"start"</td><td>Start button (start a new game)</td></tr>
    <tr><td>"exit"</td><td>Exit button (exit the simulator)</td></tr>
    <tr><td>"coin 1"</td><td>Left coin slot</td></tr>
    <tr><td>"coin 2"</td><td>Middle coin slot</td></tr>
    <tr><td>"coin 3"</td><td>Right coin slot</td></tr>
    <tr><td>"coin 4"</td><td>Fourth coin slot or bill acceptor</td></tr>
    <tr><td>"extra ball"</td><td>Extra Ball/Buy-in button</td></tr>
    <tr><td>"launch"</td><td>Launch Ball button and/or button-operated plunger</td></tr>
    <tr><td>"fire"</td><td>Fire button (button on the top of the lock bar on many later Stern machines, for activating game-specific features)</td></tr>
    <tr><td>"tilt bob"</td><td>Tilt bob switch (triggers a Tilt condition in the game; <b>not</b> for simulated nudge inputs)</td></tr>
    <tr><td>"slam tilt"</td><td>Slam tilt switch (an additional type of tilt switch inside the coin door on many real machines)</td></tr>
    <tr><td>"coin door"</td><td>Coin door open/closed position sensor switch</td></tr>
    <tr><td>"service cancel"</td><td>Cancel/Exit button, part of the service/operator control panel located inside the coin door</td></tr>
    <tr><td>"service down"</td><td>Down/Previous button, part of the service controls</td></tr>
    <tr><td>"service up"</td><td>Up/Next button, part of the service controls</td></tr>
    <tr><td>"service enter"</td>Enter/Select button, part of the service controls<td> </td></tr>
    <tr><td>"left magnasave"</td><td>Left MagnaSave button (an extra flipper-like button adjacent to the regular flipper button on some machines)</td></tr>
    <tr><td>"right magnasave"</td><td>Right MagnaSave button</td></tr>
    <tr><td>"left nudge"</td><td>Manual nudge input, simulating a nudge from the left side</td></tr>
    <tr><td>"forward nudge"</td><td>Manual nudge input, simulating a nudge pushing forward</td></tr>
    <tr><td>"right nudge"</td><td>Manual nudge input, simulating a nudge from the right side</td></tr>
    <tr><td>"volume up"</td><td>Audio volume up (controls the audio volume within the simulator; doesn't usually affect the system-wide volume level)</td></tr>
    <tr><td>"volume down"</td><td>Audio volume down</td></tr>
    <tr><td>"left flipper"</td><td>Left flipper button</td></tr>
    <tr><td>"left flipper 2"</td><td>Secondary left flipper switch, for stacked double switches used in many machines with upper</td></tr>
    <tr><td>"right flipper"</td><td>Right flipper button</td></tr>
    <tr><td>"right flipper 2"</td><td>Right secondary flipper switch, for stacked double switches</td></tr>
  </table>

  The flipper buttons are split into "main" and "secondary" switches.  These
  are designed to replicate the stacked leaf switches found in many mechanical
  pinball machines that feature upper and lower flippers.  Both switches in the
  stack are operated by a single flipper button, so there's just one left button
  and one right button.  Pushing the button part-way in closes the outer, "main"
  switch, which operates the main lower flipper on that side.  Continuing to 
  press the button further in eventually <i>also</i> closes the inner
  "secondary" switch in the stack, which operates the upper flipper on that
  side.  Many mechanical pinballs are set up this way to allow players to operate
  the upper flipper on each side separately from the lower flipper, so that
  advanced players can hold a ball trapped in a lower flipper, while separately
  using the upper flipper to take a shot with another ball during multiball play.
  If your pin cab includes the stacked switches, you can set them up as separate
  physical button inputs, and map their actions to the corresponding main and
  secondary switches here.

buttons[].action.type="key"
  This sets up the button to act as a keyboard key on the PC.  When the button
  is activated, Pinscape sends the designated key press, and keeps sending it
  as long as the button remains activated.

  To use keyboard actions, make sure that the USB keyboard device is enabled
  via the <a href="#keyboard.enable">keyboard.enable</a> property.

  A type="key" action is a very literal emulation of a physical USB keyboard
  key press, which means that it can send any <i>one</i> key, but only the
  one.  If you want send a combination of key presses involving modifier keys,
  such as Ctrl+A or Shift+Ctrl+End, you need a <a href="#buttons.action.type=macro">macro</a>.

buttons[].action.type="key".key number|string required
  Specifies the keyboard key to send when the button is pressed.  This can be
  a "usage number" from the USB HID keyboard page, from 1 to 255, or it can
  be a string giving the name of the key, from the set listed below.

  Alternatively, the key can be a "chord", which is a combination of keys with
  modifiers such as Ctrl, Shift, and Alt.  Chords are written using the Microsoft
  convention, as in "Ctrl+Shift+F1" to mean holding down the Ctrl and Shift keys
  while pressing the F1 key.  When you define a chord in this notation, the
  software internally converts the "key" action into a <a href="#buttons.action.type=macro">"macro" action</a>,
  and automatically programs the macro with a series of "key" steps matching the
  keys you list in the chord, with all of the steps starting as soon as you press
  the source button, and all of the steps remaining in effect until you release
  the source button.  So the macro steps are set to <tt>{ start: 0, duration: "hold" }</tt>.

  <table>
    <tr><th>Key name</th><th>USB usage</th><th>Description</th></tr>
    <tr><td>"a"</td><td>0x04</td><td>Keyboard a and A</td></tr>
    <tr><td>"b"</td><td>0x05</td><td>Keyboard b and B</td></tr>
    <tr><td>"c"</td><td>0x06</td><td>Keyboard c and C</td></tr>
    <tr><td>"d"</td><td>0x07</td><td>Keyboard d and D</td></tr>
    <tr><td>"e"</td><td>0x08</td><td>Keyboard e and E</td></tr>
    <tr><td>"f"</td><td>0x09</td><td>Keyboard f and F</td></tr>
    <tr><td>"g"</td><td>0x0A</td><td>Keyboard g and G</td></tr>
    <tr><td>"h"</td><td>0x0B</td><td>Keyboard h and H</td></tr>
    <tr><td>"i"</td><td>0x0C</td><td>Keyboard i and I</td></tr>
    <tr><td>"j"</td><td>0x0D</td><td>Keyboard j and J</td></tr>
    <tr><td>"k"</td><td>0x0E</td><td>Keyboard k and K</td></tr>
    <tr><td>"l"</td><td>0x0F</td><td>Keyboard l and L</td></tr>
    <tr><td>"m"</td><td>0x10</td><td>Keyboard m and M</td></tr>
    <tr><td>"n"</td><td>0x11</td><td>Keyboard n and N</td></tr>
    <tr><td>"o"</td><td>0x12</td><td>Keyboard o and O</td></tr>
    <tr><td>"p"</td><td>0x13</td><td>Keyboard p and P</td></tr>
    <tr><td>"q"</td><td>0x14</td><td>Keyboard q and Q</td></tr>
    <tr><td>"r"</td><td>0x15</td><td>Keyboard r and R</td></tr>
    <tr><td>"s"</td><td>0x16</td><td>Keyboard s and S</td></tr>
    <tr><td>"t"</td><td>0x17</td><td>Keyboard t and T</td></tr>
    <tr><td>"u"</td><td>0x18</td><td>Keyboard u and U</td></tr>
    <tr><td>"v"</td><td>0x19</td><td>Keyboard v and V</td></tr>
    <tr><td>"w"</td><td>0x1A</td><td>Keyboard w and W</td></tr>
    <tr><td>"x"</td><td>0x1B</td><td>Keyboard x and X</td></tr>
    <tr><td>"y"</td><td>0x1C</td><td>Keyboard y and Y</td></tr>
    <tr><td>"z"</td><td>0x1D</td><td>Keyboard z and Z</td></tr>
    <tr><td>"1"</td><td>0x1E</td><td>Keyboard 1 and !</td></tr>
    <tr><td>"!"</td><td>0x1E</td><td>Keyboard 1 and !</td></tr>
    <tr><td>"2"</td><td>0x1F</td><td>Keyboard 2 and @</td></tr>
    <tr><td>"@"</td><td>0x1F</td><td>Keyboard 2 and @</td></tr>
    <tr><td>"3"</td><td>0x20</td><td>Keyboard 3 and #</td></tr>
    <tr><td>"#"</td><td>0x20</td><td>Keyboard 3 and #</td></tr>
    <tr><td>"4"</td><td>0x21</td><td>Keyboard 4 and $</td></tr>
    <tr><td>"$"</td><td>0x21</td><td>Keyboard 4 and $</td></tr>
    <tr><td>"5"</td><td>0x22</td><td>Keyboard 5 and %</td></tr>
    <tr><td>"%"</td><td>0x22</td><td>Keyboard 5 and %</td></tr>
    <tr><td>"6"</td><td>0x23</td><td>Keyboard 6 and ^</td></tr>
    <tr><td>"^"</td><td>0x23</td><td>Keyboard 6 and ^</td></tr>
    <tr><td>"7"</td><td>0x24</td><td>Keyboard 7 and &</td></tr>
    <tr><td>"&"</td><td>0x24</td><td>Keyboard 7 and &</td></tr>
    <tr><td>"8"</td><td>0x25</td><td>Keyboard 8 and *</td></tr>
    <tr><td>"*"</td><td>0x25</td><td>Keyboard 8 and *</td></tr>
    <tr><td>"9"</td><td>0x26</td><td>Keyboard 9 and (</td></tr>
    <tr><td>"("</td><td>0x26</td><td>Keyboard 9 and (</td></tr>
    <tr><td>"0"</td><td>0x27</td><td>Keyboard 0 and )</td></tr>
    <tr><td>")"</td><td>0x27</td><td>Keyboard 0 and )</td></tr>
    <tr><td>"return"</td><td>0x28</td><td>Keyboard Return (ENTER)</td></tr>
    <tr><td>"enter"</td><td>0x28</td><td>Keyboard Return (ENTER)</td></tr>
    <tr><td>"esc"</td><td>0x29</td><td>Keyboard ESCAPE</td></tr>
    <tr><td>"escape"</td><td>0x29</td><td>Keyboard ESCAPE</td></tr>
    <tr><td>"backspace"</td><td>0x2A</td><td>Keyboard DELETE (Backspace)</td></tr>
    <tr><td>"bksp"</td><td>0x2A</td><td>Keyboard DELETE (Backspace)</td></tr>
    <tr><td>"tab"</td><td>0x2B</td><td>Keyboard Tab</td></tr>
    <tr><td>"space"</td><td>0x2C</td><td>Keyboard Spacebar</td></tr>
    <tr><td>"spacebar"</td><td>0x2C</td><td>Keyboard Spacebar</td></tr>
    <tr><td>"-"</td><td>0x2D</td><td>Keyboard - and (underscore)</td></tr>
    <tr><td>"_"</td><td>0x2D</td><td>Keyboard - and (underscore)</td></tr>
    <tr><td>"hyphen"</td><td>0x2D</td><td>Keyboard - and (underscore)</td></tr>
    <tr><td>"minus"</td><td>0x2D</td><td>Keyboard - and (underscore)</td></tr>
    <tr><td>"="</td><td>0x2E</td><td>Keyboard = and +</td></tr>
    <tr><td>"+"</td><td>0x2E</td><td>Keyboard = and +</td></tr>
    <tr><td>"equals"</td><td>0x2E</td><td>Keyboard = and +</td></tr>
    <tr><td>"["</td><td>0x2F</td><td>Keyboard [ and {</td></tr>
    <tr><td>"{"</td><td>0x2F</td><td>Keyboard [ and {</td></tr>
    <tr><td>"lbrack"</td><td>0x2F</td><td>Keyboard [ and {</td></tr>
    <tr><td>"lbrace"</td><td>0x2F</td><td>Keyboard [ and {</td></tr>
    <tr><td>"]"</td><td>0x30</td><td>Keyboard ] and }</td></tr>
    <tr><td>"}"</td><td>0x30</td><td>Keyboard ] and }</td></tr>
    <tr><td>"rbrack"</td><td>0x30</td><td>Keyboard ] and }</td></tr>
    <tr><td>"rbrace"</td><td>0x30</td><td>Keyboard ] and }</td></tr>
    <tr><td>"\\"</td><td>0x31</td><td>Keyboard \ and |</td></tr>
    <tr><td>"||"</td><td>0x31</td><td>Keyboard \ and |</td></tr>
    <tr><td>"backslash"</td><td>0x31</td><td>Keyboard \ and |</td></tr>
    <tr><td>";"</td><td>0x33</td><td>Keyboard ; and :</td></tr>
    <tr><td>":"</td><td>0x33</td><td>Keyboard ; and :</td></tr>
    <tr><td>"semicolon"</td><td>0x33</td><td>Keyboard ; and :</td></tr>
    <tr><td>"colon"</td><td>0x33</td><td>Keyboard ; and :</td></tr>
    <tr><td>"'"</td><td>0x34</td><td>Keyboard ' and "</td></tr>
    <tr><td>"\""</td><td>0x34</td><td>Keyboard ' and "</td></tr>
    <tr><td>"grave"</td><td>0x35</td><td>Keyboard ` and ~</td></tr>
    <tr><td>"tilde"</td><td>0x35</td><td>Keyboard ` and ~</td></tr>
    <tr><td>"`"</td><td>0x35</td><td>Keyboard ` and ~</td></tr>
    <tr><td>"~"</td><td>0x35</td><td>Keyboard ` and ~</td></tr>
    <tr><td>","</td><td>x36</td><td>Keyboard , and <</td></tr>
    <tr><td>"<"</td><td>0x36</td><td>Keyboard , and <</td></tr>
    <tr><td>"comma"</td><td>x36</td><td>Keyboard , and <</td></tr>
    <tr><td>"."</td><td>0x37</td><td>Keyboard . and ></td></tr>
    <tr><td>">"</td><td>0x37</td><td>Keyboard . and ></td></tr>
    <tr><td>"period"</td><td>0x37</td><td>Keyboard . and ></td></tr>
    <tr><td>"dot"</td><td>0x37</td><td>Keyboard . and ></td></tr>
    <tr><td>"/"</td><td>0x38</td><td>Keyboard / and ?</td></tr>
    <tr><td>"?"</td><td>0x38</td><td>Keyboard / and ?</td></tr>
    <tr><td>"slash"</td><td>0x38</td><td>Keyboard / and ?</td></tr>
    <tr><td>"caps lock"</td><td>0x39</td><td>Keyboard Caps Lock</td></tr>
    <tr><td>"capslock"</td><td>0x39</td><td>Keyboard Caps Lock</td></tr>
    <tr><td>"f1"</td><td>0x3A</td><td>Keyboard F1</td></tr>
    <tr><td>"f2"</td><td>0x3B</td><td>Keyboard F2</td></tr>
    <tr><td>"f3"</td><td>0x3C</td><td>Keyboard F3</td></tr>
    <tr><td>"f4"</td><td>0x3D</td><td>Keyboard F4</td></tr>
    <tr><td>"f5"</td><td>0x3E</td><td>Keyboard F5</td></tr>
    <tr><td>"f6"</td><td>0x3F</td><td>Keyboard F6</td></tr>
    <tr><td>"f7"</td><td>0x40</td><td>Keyboard F7</td></tr>
    <tr><td>"f8"</td><td>0x41</td><td>Keyboard F8</td></tr>
    <tr><td>"f9"</td><td>0x42</td><td>Keyboard F9</td></tr>
    <tr><td>"f10"</td><td>0x43</td><td>Keyboard F10</td></tr>
    <tr><td>"f11"</td><td>0x44</td><td>Keyboard F11</td></tr>
    <tr><td>"f12"</td><td>0x45</td><td>Keyboard F12</td></tr>
    <tr><td>"print screen"</td><td>0x46</td><td>Keyboard PrintScreen</td></tr>
    <tr><td>"printscreen"</td><td>0x46</td><td>Keyboard PrintScreen</td></tr>
    <tr><td>"prntscrn"</td><td>0x46</td><td>Keyboard PrintScreen</td></tr>
    <tr><td>"prtscr"</td><td>0x46</td><td>Keyboard PrintScreen</td></tr>
    <tr><td>"scrolllock"</td><td>0x47</td><td>Keyboard Scroll Lock</td></tr>
    <tr><td>"scroll lock"</td><td>0x47</td><td>Keyboard Scroll Lock</td></tr>
    <tr><td>"pause"</td><td>0x48</td><td>Keyboard Pause</td></tr>
    <tr><td>"ins"</td><td>0x49</td><td>Keyboard Insert</td></tr>
    <tr><td>"insert"</td><td>0x49</td><td>Keyboard Insert</td></tr>
    <tr><td>"home"</td><td>0x4A</td><td>Keyboard Home</td></tr>
    <tr><td>"page up"</td><td>0x4B</td><td>Keyboard PageUp</td></tr>
    <tr><td>"pageup"</td><td>0x4B</td><td>Keyboard PageUp</td></tr>
    <tr><td>"pgup"</td><td>0x4B</td><td>Keyboard PageUp</td></tr>
    <tr><td>"del"</td><td>0x4C</td><td>Keyboard Delete Forward</td></tr>
    <tr><td>"delete"</td><td>0x4C</td><td>Keyboard Delete Forward</td></tr>
    <tr><td>"end"</td><td>0x4D</td><td>Keyboard End</td></tr>
    <tr><td>"page down"</td><td>0x4E</td><td>Keyboard PageDown</td></tr>
    <tr><td>"pagedown"</td><td>0x4E</td><td>Keyboard PageDown</td></tr>
    <tr><td>"pagedn"</td><td>0x4E</td><td>Keyboard PageDown</td></tr>
    <tr><td>"pgdn"</td><td>0x4E</td><td>Keyboard PageDown</td></tr>
    <tr><td>"right"</td><td>0x4F</td><td>Keyboard RightArrow</td></tr>
    <tr><td>"right arrow"</td><td>0x4F</td><td>Keyboard RightArrow</td></tr>
    <tr><td>"left"</td><td>0x50</td><td>Keyboard LeftArrow</td></tr>
    <tr><td>"left arrow"</td><td>0x50</td><td>Keyboard LeftArrow</td></tr>
    <tr><td>"down"</td><td>0x51</td><td>Keyboard DownArrow</td></tr>
    <tr><td>"down arrow"</td><td>0x51</td><td>Keyboard DownArrow</td></tr>
    <tr><td>"up"</td><td>0x52</td><td>Keyboard UpArrow</td></tr>
    <tr><td>"up arrow"</td><td>0x52</td><td>Keyboard UpArrow</td></tr>
    <tr><td>"numlock"</td><td>0x53</td><td>Keypad Num Lock and Clear</td></tr>
    <tr><td>"num lock"</td><td>0x53</td><td>Keypad Num Lock and Clear</td></tr>
    <tr><td>"clear"</td><td>0x53</td><td>Keypad Num Lock and Clear</td></tr>
    <tr><td>"keypad /"</td><td>0x54</td><td>Keypad /</td></tr>
    <tr><td>"keypad *"</td><td>0x55</td><td>Keypad *</td></tr>
    <tr><td>"keypad -"</td><td>0x56</td><td>Keypad -</td></tr>
    <tr><td>"keypad +"</td><td>0x57</td><td>Keypad +</td></tr>
    <tr><td>"keypad enter"</td><td>0x58</td><td>Keypad ENTER</td></tr>
    <tr><td>"keypad 1"</td><td>0x59</td><td>Keypad 1 and End</td></tr>
    <tr><td>"keypad 2"</td><td>0x5A</td><td>Keypad 2 and Down Arrow</td></tr>
    <tr><td>"keypad 3"</td><td>0x5B</td><td>Keypad 3 and PageDn</td></tr>
    <tr><td>"keypad 4"</td><td>0x5C</td><td>Keypad 4 and Left Arrow</td></tr>
    <tr><td>"keypad 5"</td><td>0x5D</td><td>Keypad 5</td></tr>
    <tr><td>"keypad 6"</td><td>0x5E</td><td>Keypad 6 and Right Arrow</td></tr>
    <tr><td>"keypad 7"</td><td>0x5F</td><td>Keypad 7 and Home</td></tr>
    <tr><td>"keypad 8"</td><td>0x60</td><td>Keypad 8 and Up Arrow</td></tr>
    <tr><td>"keypad 9"</td><td>0x61</td><td>Keypad 9 and PageUp</td></tr>
    <tr><td>"keypad 0"</td><td>0x62</td><td>Keypad 0 and Insert</td></tr>
    <tr><td>"keypad ."</td><td>0x63</td><td>Keypad . and Delete</td></tr>
    <tr><td>"application"</td><td>0x65</td><td>Keyboard Application</td></tr>
    <tr><td>"power"</td><td>0x66</td><td>Keyboard Power</td></tr>
    <tr><td>"keypad ="</td><td>0x67</td><td>Keypad =</td></tr>
    <tr><td>"f13"</td><td>0x68</td><td>Keyboard F13</td></tr>
    <tr><td>"f14"</td><td>0x69</td><td>Keyboard F14</td></tr>
    <tr><td>"f15"</td><td>0x6A</td><td>Keyboard F15</td></tr>
    <tr><td>"f16"</td><td>0x6B</td><td>Keyboard F16</td></tr>
    <tr><td>"f17"</td><td>0x6C</td><td>Keyboard F17</td></tr>
    <tr><td>"f18"</td><td>0x6D</td><td>Keyboard F18</td></tr>
    <tr><td>"f19"</td><td>0x6E</td><td>Keyboard F19</td></tr>
    <tr><td>"f20"</td><td>0x6F</td><td>Keyboard F20</td></tr>
    <tr><td>"f21"</td><td>0x70</td><td>Keyboard F21</td></tr>
    <tr><td>"f22"</td><td>0x71</td><td>Keyboard F22</td></tr>
    <tr><td>"f23"</td><td>0x72</td><td>Keyboard F23</td></tr>
    <tr><td>"f24"</td><td>0x73</td><td>Keyboard F24</td></tr>
    <tr><td>"execute"</td><td>0x74</td><td>Keyboard Execute</td></tr>
    <tr><td>"help"</td><td>0x75</td><td>Keyboard Help</td></tr>
    <tr><td>"menu"</td><td>0x76</td><td>Keyboard Menu</td></tr>
    <tr><td>"select"</td><td>0x77</td><td>Keyboard Select</td></tr>
    <tr><td>"stop"</td><td>0x78</td><td>Keyboard Stop</td></tr>
    <tr><td>"again"</td><td>0x79</td><td>Keyboard Again</td></tr>
    <tr><td>"undo"</td><td>0x7A</td><td>Keyboard Undo</td></tr>
    <tr><td>"cut"</td><td>0x7B</td><td>Keyboard Cut</td></tr>
    <tr><td>"copy"</td><td>0x7C</td><td>Keyboard Copy</td></tr>
    <tr><td>"paste"</td><td>0x7D</td><td>Keyboard Paste</td></tr>
    <tr><td>"find"</td><td>0x7E</td><td>Keyboard Find</td></tr>
    <tr><td>"mute"</td><td>0x7F</td><td>Keyboard Mute</td></tr>
    <tr><td>"volup"</td><td>0x80</td><td>Keyboard Volume Up</td></tr>
    <tr><td>"voldown"</td><td>0x81</td><td>Keyboard Volume Down</td></tr>
    <tr><td>"voldn"</td><td>0x81</td><td>Keyboard Volume Down</td></tr>
    <tr><td>"keypad ,"</td><td>0x85</td><td>Keypad Comma</td></tr>
    <tr><td>"keypad comma"</td><td>0x85</td><td>Keypad Comma</td></tr>
    <tr><td>"keypad 00"</td><td>0xB0</td><td>Keypad 00</td></tr>
    <tr><td>"keypad 000"</td><td>0xB1</td><td>Keypad 000</td></tr>
    <tr><td>"ctrl"</td><td>0xE0</td><td>Keyboard LeftControl</td></tr>
    <tr><td>"left ctrl"</td><td>0xE0</td><td>Keyboard LeftControl</td></tr>
    <tr><td>"left control"</td><td>0xE0</td><td>Keyboard LeftControl</td></tr>
    <tr><td>"shift"</td><td>0xE1</td><td>Keyboard LeftShift</td></tr>
    <tr><td>"left shift"</td><td>0xE1</td><td>Keyboard LeftShift</td></tr>
    <tr><td>"alt"</td><td>0xE2</td><td>Keyboard LeftAlt</td></tr>
    <tr><td>"left alt"</td><td>0xE2</td><td>Keyboard LeftAlt</td></tr>
    <tr><td>"gui"</td><td>0xE3</td><td>Keyboard Left GUI</td></tr>
    <tr><td>"left gui"</td><td>0xE3</td><td>Keyboard Left GUI</td></tr>
    <tr><td>"right ctrl"</td><td>0xE4</td><td>Keyboard RightControl</td></tr>
    <tr><td>"right control"</td><td>0xE4</td><td>Keyboard RightControl</td></tr>
    <tr><td>"right shift"</td><td>0xE5</td><td>Keyboard RightShift</td></tr>
    <tr><td>"right alt"</td><td>0xE6</td><td>Keyboard RightAlt</td></tr>
    <tr><td>"right gui"</td><td>0xE7</td><td>Keyboard Right GUI</td></tr>
  </table>

buttons[].action.type="media"
  This sets up the button to act as a "media controller" key on the PC.
  These are essentially just an extended set of keyboard keys associated with
  media functions, like "Play" and "Pause", which appear on some keyboards as
  an extra row of keys above the function keys.

  To use media key actions, make sure that the USB keyboard device is enabled
  via the <a href="#keyboard.enable">keyboard.enable</a> property.

buttons[].action.type="media".key string{table} required
  Specifies the media key to send when the button is pressed.  This is
  a string naming one of the special media keys that Pinscape can send.
  <table>
    <tr><th>Key name</th><th>Description</td></tr>
    <tr><td>"mute"</td><td>Mute audio</td></tr>
    <tr><td>"volUp"</td><td>Audio volume up</td></tr>
    <tr><td>"volDn"</td><td>Audio volume down</td></tr>
    <tr><td>"next"</td><td>Skip to next media track</td></tr>
    <tr><td>"prev"</td><td>Skip to previous media track</td></tr>
    <tr><td>"stop"</td><td>Stop media playback</td></tr>
    <tr><td>"play"</td><td>Start media playback</td></tr>
    <tr><td>"eject"</td><td>Eject media (note: Windows ignores this key)</td></tr>
  </table>

buttons[].action.type="gamepad"
  Sets up the button to act as a gamepad button on the PC.  Activating the
  logical button presses the associated gamepad button.

buttons[].action.type="gamepad".button number|string required
  The gamepad button number to press when the logical button is activated, 1 to 32,
  <i>or</i> a string from the list below.
  <table>
    <tr><th>String Value</th><th>Description</td></tr>
    <tr><td>hat-down</td><td>Hat switch "down" (south) button</td></tr>
    <tr><td>hat-left</td><td>Hat switch "left" (west) button</td></tr>
    <tr><td>hat-right</td><td>Hat switch "right" (east) button</td></tr>
    <tr><td>hat-up</td><td>Hat switch "up" (north) button</td></tr>
  </table>

buttons[].action.type="xInput"
  Sets up the button to act as an XBox controller button on the PC.  Activating
  the logical button presses the associated XBox controller button.

buttons[].action.type="xInput".button string{table} required
  The XBox controller button to press when the logical button is activated.
  <table>
    <tr><th>Key name</th><th>Description</th>
    <tr><td>"up"</td><td>Direction pad UP button</td></tr>
    <tr><td>"down"</td><td>Direction pad DOWN button</td></tr>
    <tr><td>"left"</td><td>Direction pad LEFT button</td></tr>
    <tr><td>"right"</td><td>Direction pad RIGHT button</td></tr>
    <tr><td>"start"</td><td>START button</td></tr>
    <tr><td>"back"</td><td>BACK button</td></tr>
    <tr><td>"l3"</td><td>Left joystick click</td></tr>
    <tr><td>"r3"</td><td>Right joystick click</td></tr>
    <tr><td>"lb"</td><td>Left bumper button (back of controller)</td></tr>
    <tr><td>"rb"</td><td>Right bumper button (back of controller)</td></tr>
    <tr><td>"xbox"</td><td>XBOX button</td></tr>
    <tr><td>"a"</td><td>A button</td></tr>
    <tr><td>"b"</td><td>B button</td></tr>
    <tr><td>"x"</td><td>X button</td></tr>
    <tr><td>"y"</td><td>Y button</td></tr>
  </table>

buttons[].action.type="reset"
  Activating the button resets the Pico, optionally activating its Boot Loader mode.

buttons[].action.type="reset".mode string{table} optional
  Reset mode.  This is a string specifying the mode the Pico enters after the reset.
  The default if <tt>type</tt> isn't specified is "normal".
  <table>
    <tr><th>Type name</th><th>Description</th></tr>
    <tr>
      <td>"normal"</td>
      <td>Restarts the Pinscape firmware currently stored in the Pico's flash memory.  This is the default.</td>
    </tr>
    <tr>
      <td>"bootloader"</td>
      <td>Restarts the Pico in Boot Loader mode, where it appears as a virtual USB thumb drive that will accept new firmware via a .UF2 file transfer.</td>
    </tr>
    <tr>
      <td>"safe"</td>
      <td>
        Reboots into Safe Mode.  This restarts the Pinscape firmware, but loads the Safe Mode configuration instead of the normal JSON configuration.
        Safe Mode is normally invoked if the Pinscape software crashes or the Pico unexpectedly resets, but it can also be useful
        to invoke deliberately if you want to bypass the normal configuration settings.
      </td>
    </tr>
    <tr>
      <td>"factory"</td>
      <td>
        Reboots into Factory Mode.  This is similar to Safe Mode, except that it doesn't load any JSON configuration settings,
        and instead uses defaults for all settings.  This is the basic configuration that you get with a new Pico that
        you haven't customized with any JSON settings yet.
      </td>
    </tr>
  </table>

buttons[].action.type="reset".holdTime number optional
  The time the button must be held down, in milliseconds, before the reset
  occurs.  Default is 2000ms (2 seconds).

buttons[].action.type="nightmode"
  Sets up the button as a Night Mode control.  The specific way that
  the button controls Night Mode depends upon the <tt>action.mode</tt>
  property.

buttons[].action.type="nightmode".mode string{table} optional
  Selects how the button action controls Night Mode.  If not
  specified, the default is "follow".
  <table>
    <tr><th><tt>mode</tt> value</th><th>Description</th></tr>
    <tr><td>"follow"</td><td>Night Mode follows the state of the button: each time the button state changes to ON, Night Mode is activated, and each time the button state changes to OFF, Night Mode is deactivated</td></tr>
    <tr><td>"toggle"</td><td>Toggles Night Mode ON or OFF each time the button is pressed (that is, each time the button state changes from OFF to ON)</td></tr>
    <tr><td>"set"</td><td>Activates Night Mode each time the button is pressed (when the button state changes from OFF to ON)</td></tr>
    <tr><td>"clear"</td><td>Deactivates Night Mode each time the button is pressed (when the button state changes from OFF to ON)</td></tr>
  </table>

  The "follow" mode is most useful with a physical toggle switch,
  where you want Night Mode to be ON when you flip the switch to the
  ON position, and OFF when you flip the switch OFF.  It can be used
  just as well with a logical toggle button, although in that case
  you can just use the "toggle" mode instead.  The "set" and "clear"
  modes could be useful if you want separate ON and OFF buttons, so
  that you can always make sure Night Mode is engaged or disengaged
  with a single button press, without having to remember (or figure
  out) whether it's already on.

  For "toggle" mode, if the button you're using has an indicator
  light, you could wire the indicator light to a Pinscape output
  port that's set to <tt>source: "nightmode(255,0)"</tt>.  That
  will make the button indicator light up when Night Mode is
  engaged, so that you can see just by looking at the button if
  Night Mode is in effect.

buttons[].action.type="plungercal"
  Sets up the button to act as the plunger calibration mode control
  button.  Pressing and holding the button for about two seconds 
  activates calibration mode.  Once calibration mode is initiated, the 
  calibration runs for a set time (about 15 seconds) to gather data on 
  the range of sensor readings over the plunger's mechanical travel distance.
  During this period, the user should pull the plunger all the way back, hold 
  it briefly, release it, allow it to come to rest, and then repeat a few times.  
  When the timed interval ends, the new calibration settings automatically 
  go into effect.

buttons[].action.type="IR"
  Sets up the button to transmit a remote control command through the
  IR emitter when pressed.

buttons[].action.type="IR".code string required
  The IR command code to send when the button is pressed, expressed as a
  string in the Pinscape universal IR code format.  The easiest way to
  determine the right code to use for a particular button press is to
  use the Pinscape Config Tool's IR & TV ON window, which displays codes
  as they're received on the sensor.  Open the window and press the remote
  control button whose code you want to determine, and it should appear in
  the list of commands received.  Now simply copy the code from that list
  into the type string here.

buttons[].action.type="IR".autoRepeat bool optional
  If set to true, the IR command is sent repeatedly as long as the logical
  button is activated.  If false (the default), the command is only sent
  once when the logical button is pressed, no longer how long the button
  remains activated.

buttons[].action.type="macro"
  EXAMPLE:
  {
     buttons: [
        {
           type: "push",
           source: { type: "gpio", port: 7 },
           action: {
              type: "macro",
              steps: [
                 // This macro sends sends a Shift+Ctrl+A to the PC.  We have
                 // to engage the modifier keys first, pause briefly to let the
                 // PC see the modifier keys, then press the "A" key while
                 // still holding the modifier keys down.
                 { start: 0, duration: "hold", action: { type: "key", key: "left shift" }, },  // hold SHIFT until button released
                 { start: 0, duration: "hold", action: { type: "key", key: "left ctrl" }, },   // hold CTRL at the same time, until button released
                 { start: 10, duration: "hold", action: { type: "key", key: "A" }, },          // wait 10ms, then press A, and hold until button released
              ],
           },
        },
     ],
  }

  This sets up a macro button, which performs a series of timed actions
  when activated.

  A macro can carry out any sequence of other basic actions, with the
  exception that it can't invoke another macro.  This allows for all
  sorts of complex actions, such as pressing chords of keyboard keys
  (Ctrl+Shift+A, say), typing in a sequence of keystrokes to enter
  a command, pushing a joystick button and a keyboard key at the
  same time, or entering a series of joystick button presses.

  The macro is defined as a series of steps to perform.  Each step
  has a starting time relative to the previous step's starting time.
  This can be zero, in which case the step starts at the same time
  as the previous step.  Each step also has a duration, which specifies
  how long the action goes on; for example, for a key press action,
  this specifies how long the key is held down.

  A macro can be set to repeat its series of steps as long as the
  physical button is held down, or to just execute it once and then
  stop, even if the user continues to press the button indefinitely.
  Similarly, you can specify whether the macro runs to completion once
  started, even if the user doesn't keep holding down the button long
  enough to complete the macro, or if the macro stops in the middle of
  what it's doing when the user releases the button.

buttons[].action.type="macro".runToCompletion bool optional
  If set to true (the default), the macro runs through all of its steps
  every time the button is pressed, even if the button isn't held down
  as long as it takes to finish running through the steps.  If set to
  false, the macro stops as soon as the button is released, even if
  there are still more steps that haven't been completed yet.

buttons[].action.type="macro".repeat bool optional
  If set to true (the default), the macro will start over at the beginning
  if the button is still being held down after the last step finishes.
  If set to false, the macro only runs once, stopping after the last step
  even if the button is still being held down.

buttons[].action.type="macro".steps [object] required
  An array of objects giving the list of action steps to carry out when the
  button is pressed.  Each step lists one action, with a starting time and
  a duration.  Each step's action is an object with exactly the same properties
  as the main "action" property for a button, so in effect, a macro carries out
  the equivalent of a series of timed button presses.  But the "buttons"
  being pressed don't have to exist outside of the macro, since the macro
  contains the entire definition of each action.

buttons[].action.type="macro".steps[].start number optional
  The starting time of the step, as the number of milliseconds to wait after the
  start of the previous step.  If this is zero (the default), this step starts
  simultaneously with the previous step.  Note that the reference point is the
  starting time of the prior step, which lets you start multiple steps at the
  same time - a new step doesn't have to wait until the prior step finishes.

buttons[].action.type="macro".steps[].duration number|string required
  The duration of the step, in milliseconds, <b>or</b> the special string value
  <tt>"hold"</tt>.  This is the amount of time that the step's action remains
  activated.  A step can remain activated even while later steps are started;
  new steps don't have to wait for earlier steps to finish.

  If this is set to <tt>"hold"</tt>, it means that the step remains in effect
  until the button that activated the macro is released.  This makes it easy
  to define a macro that expresses a "key chord" such as Ctrl+Alt+X, by letting
  you program the macro to hold all three key actions as long as the button is
  being pressed.

buttons[].action.type="macro".steps[].action object<buttons.action> required
  The action to perform.  This is the same sort of action object that you can
  define for a button in its "action" property, with all of the same properties,
  except that it can't contain another macro action.

buttons[].action.type="none"
  This sets up a virtual button that accepts input but doesn't perform any action.

buttons[].shiftMask number optional
  Sets the bits in the "global shift state" that the button is sensitive to.

  When the button is pressed, Pinscape combines this button's shiftMask with the
  current global shift state using a bitwise AND.  It then compares the result
  to the button's <a href="#shiftBits">shiftBits</a>.  If the two values are
  equal, the press activates the button.  Otherwise, the press is ignored.

  This can be used to make a button sensitive to one or more modifier buttons,
  or to make it insensitive to all of the modifier buttons.  The table below
  lists some basic formulas for how to set this up (in combination with shiftBits) 
  to get different effects.  For the examples in the table, let's say that we've 
  set up the following shift buttons:
  
  <ul>
     <li>EXTRA BALL - shiftBits: 0x0001</li>
     <li>EXIT - shiftBits: 0x0002</li>
  </ul>

  You can easily extend this idea to add as many more shift buttons as you need,
  up to a total of 32 of them.  Just keep picking the next higher bit value for each
  added button: 0x0004, 0x0008, 0x0010, etc.

  <table>
    <tr><th>Goal</th><th>shiftMask</th><th>shiftBits</th><th>Description</th></tr>
    <tr>
       <td>Ignores all shift buttons</td>
       <td>0</td>
       <td>0</td>
       <td>
         This button always works the same way, regardless of which shift buttons are pressed.
         Since X AND 0 = 0 for all X, the result of shiftMask AND global-shift-state is always
         0, so it always matches the zero in shiftBits, and the button always operates.
       </td>
    </tr>
    <tr>
       <td>Operates when EXTRA BALL <b>is not</b> pressed</td>
       <td>0x0001</td>
       <td>0x0000</td>
       <td>
         This button only takes effect when the EXTRA BALL shift button is NOT pressed.
         When EXTRA BALL is pressed, the global shift state contains EXTRA BALL's
         shiftBits bits, 0x0001, so shiftMask AND global-shift-state equals 0x0001.
         This is <b>not</b> equal to shiftBits, so the button ignores the press.
         When EXTRA BALL <b>isn't</b> pressed, the global shift state doesn't
         contain bit 0x0001, so shiftMask AND global-shift-state equals 0, which
         equals the shiftBits value, so the button activates.
       </td>
     </tr>
    <tr>
       <td>Operates when EXTRA BALL <b>is</b> pressed</td>
       <td>0x0001</td>
       <td>0x0001</td>
       <td>
         This button only takes effect when the EXTRA BALL shift button is pressed.
         When EXTRA BALL is pressed, the global shift state contains EXTRA BALL's
         shiftBits bits, 0x0001, so shiftMask AND global-shift-state equals 0x0001.
         This equals shiftBits, so the button activates.
         When EXTRA BALL <b>isn't</b> pressed, the global shift state doesn't
         contain bit 0x0001, so shiftMask AND global-shift-state equals 0, which
         is unequal to shiftBits, so the button ignores the press.
         <p>Note that this button ignores the EXIT button state - it only pays
         attention to the EXTRA BALL state.</p>
       </td>
     </tr>
    <tr>
       <td>Operates when <b>both</b> EXTRA BALL and EXIT are pressed</td>
       <td>0x0003</td>
       <td>0x0003</td>
       <td>
         This is how you create a chord analogous to Alt+Ctrl+X on a PC keyboard.
         This button takes effect only when BOTH shift keys are pressed.  This
         works because the shiftMask contains the combination of shift bits for
         both of the modifier keys - 0x0001 OR 0x0002 = 0x0003.  When we figure
         global-shift-state AND shiftMask, we get 0x0003 (the shiftBits value)
         only if the global shift state contains both of those bits, so the
         button only operates if both modifiers are pressed.
       </td>
     </tr>
    <tr>
       <td>Operates when EXTRA BALL is pressed but <b>not</b> EXIT</td>
       <td>0x0003</td>
       <td>0x0001</td>
       <td>
         This is the flip side of the EXTRA BALL + EXIT case above, setting
         the button so that it only operates when one of the modifier keys
         is pressed, <i>but not both</i>.  shiftMask contains the bits for both of the shift keys,
         but shiftBits only contains the bits for EXTRA BALL, so the button
         will only operate when EXTRA BALL is pressed and EXIT is not.
         (To define a button that operates when EXIT is pressed but not
         EXTRA BALL, change shiftBits to 0x0002, the EXIT shift bits.)
       </td>
     </tr>
  </table>

  shiftMask has no effect for a button that's defined with type "shift".
  Shift buttons always mean one thing and always ignore other shift buttons.

buttons[].shiftBits number optional
  For a button with <a href="#buttons.type=shift">type="shift"</a>, this sets
  the bits that are added into the "global shift state" when the button is
  pressed.

  For any other button type, this sets the value that the following formula
  must match each time the button is pressed for the button to activate:

  <tt>global-shift-state AND shiftMask == shiftBits</tt>

  See <a href="#buttons.shiftMask">shiftMask</a> for more details on how
  the shift bits and shift mask work together to determine how the button
  reacts to modifier buttons.
    

buttons[].type string{table} optional
  The logical button type, which determines how On/Off state changes on the
  underlying physical button input are interpreted for the logical button.
  The default is "push", which is an ordinary momentary pushbutton.
  <table>
    <tr><th>Type name</th><th>Description</th></tr>
    <tr><td>"push"</td><td>This is the default; an ordinary momentary pushbutton.  The logical action is activated for as long as the underlying physical button is pressed.</td></tr>
    <tr><td>"hold"</td><td>The action doesn't take effect until the underlying button has been held down for a specified minimum interval; after that, it acts like an ordinary pushbutton, with the action activated until the button is released</td></tr>
    <tr><td>"pulse"</td><td>When the underlying physical button is pressed, the action is activated briefly, for the "on" pulse time; then nothing happens until the button is released, at which point the action is pulsed again, for the "off" time period</td></tr>
    <tr><td>"toggle"</td><td>Each time the underlying physical button is pressed, the action is toggled between ON and OFF</td></tr>
    <tr><td>"shift"</td><td>This button acts as a modifier for other buttons, by turn its "shift bits" on as long as it's being pressed</td></tr>
  </table>

buttons[].type="push"
  This is the default button type, which acts like an ordinary momentary pushbutton.
  Pressing the button activates the button's action for as long as the button is being
  pressed, and the action deactivates as soon as the button is released.

buttons[].type="hold"
  A "hold" button is like an ordinary pushbutton, except that its action isn't activated
  until the button has been held down for a set amount of time.  This can be used for
  buttons that have some kind of significant effect that you wouldn't want to be triggered
  accidentally, such as shutting down the computer or rebooting the Pico.  The hold time
  helps ensure that the user really meant to push the button by forcing them to hold it
  down for a few moments before anything happens.  It's the physical control panel
  analog of a Windows "Are You Sure...?" dialog box.

  Optionally, a hold button can also define an action to carry out after a "short press",
  when the button is pressed and then released before the hold period ends.  By default,
  a short press on a hold button has no effect at all, since the main action isn't
  triggered until the button has been held down for the full hold period.  If the button
  has a short-press action defined, though, the button triggers an action on every press:
  the short-press action when the button is released before the hold period ends, and
  the normal action otherwise.  This can be used an alternative to the "Shift" button
  scheme when you want to make one physical button serve dual purposes.  In this case,
  the user selects which of the two functions should be performed via the duration
  of the button press.

buttons[].type="hold".holdTime number optional
  The hold time before the button's action takes effect, in milliseconds (1000 milliseconds
  equals one second).  If you omit the hold time, the default is 2000 (which amounts to 2 seconds).

buttons[].type="hold".shortPress object optional
  This defines an action to carry out after a "short press", where the user presses
  the button and then releases it before the holding period is reached.  By default,
  a hold button doesn't do anything at all on a short press, since the whole point of
  the holding period is to require the user to hold the button long enough to ensure
  that the press was intentional.  The <tt>shortPress</tt> option lets you define an
  alternative action that fires <i>only</i> when the button <i>isn't</i> held down
  for the defined holding period.

  The short press action isn't fired until the button is <i>released</i>, because
  there's no way to know until then that this will in fact be a short press.
  Only one action will fire on a given press - either the short press action or the
  main action, never both.  When the button is held down past the holding time,
  the normal action will fire as soon as the holding time passes, and the short-press
  action will <i>not</i> fire when the button is released.

buttons[].type="hold".shortPress.action object<buttons.action> optional
  SEE: buttons.action
  Sets the action to carry out after a short press (that is, when the user presses
  and then releases the button before the hold time is reached).  This action is
  carried out <i>when the button is released</i>, and only when it's released
  before the hold time is reached.  Once the hold time is reached, the main action
  fires, and the short-press action is ignored for that button press event.

buttons[].type="hold".shortPress.actionTime number optional
  Sets the duration in milliseconds of the short-press action, once fired.  With
  normal button actions, the duration of the action is controlled by how long you
  keep pressing the button.  But that's not applicable to a short-press action,
  because a short-press action isn't fired until the user <i>releases</i> the
  button, meaning that there's no "natural" end time for the action.  Instead,
  the action fires for the fixed duration specified here.  The default setting
  if you omit this property is 20 milliseconds, which was chosen because it
  should be long enough for the PC to reliably detect and process the action,
  but not so long that the PC will think it needs to auto-repeat the action
  (which it might do with actions like keyboard key-presses, for example).

buttons[].type="pulse"
  A "pulse" button executes its action briefly when you press the button, and then
  sits there quietly until you release the button, at which point it executes the
  action again, briefly.  The "pulse" is the brief period when the action is
  executed at each end of the button push.  The on and off pulse times can be
  set individually.  If you set one of the pulse times to zero, the action won't
  be executed at all at that end of the push.  For example, if you set the off
  pulse time to zero, the action is only executed when the button is pushed,
  and nothing more happens when the button is released.  Pulse buttons are especially
  useful when the physical source button is an On/Off switch rather than a momentary
  button, but the program on the Windows side expects a single key press (or something
  similar) only when the switch changes state.  The canonical example is the Coin 
  Door switch, which is typically implemented as a switch that's engaged whenever
  the door is closed, but which some pinball programs simulate using a key press
  to toggle the program's notion of the door between open and closed.  This can
  be done easily with a pulse button, since it executes its action (which can be
  set to the pinball program's Coin Door keyboard key for this example) each
  time the underlying physical door switch changes between On and Off.

buttons[].type="pulse".tOn number optional
  Sets the time for the button's "on" pulse, which is the amount of time that the
  button activates its action when the underlying physical input button changes
  from OFF to ON.  The time is in milliseconds (1000 milliseconds equals one second).
  If you set this to zero, nothing at all happens when the OFF-to-ON transition occurs.
  The default is 100 milliseconds (about 1/10th of a second).

buttons[].type="pulse".tOff number optional
  Sets the time for the button's "off" pulse, which is the amount of time that the
  button activates its action when the underlying physical input button changes
  from ON to OFF.  The time is in milliseconds (1000 milliseconds equals one second).
  If you set this to zero, nothing at all happens when the ON-to-OFF transition occurs.
  The default is zero.

buttons[].type="pulse".tSpace number optional
  Sets the minimum time delay between pulses of the button.  If you press and release
  the button faster than this, the button will wait until the spacer time has passed
  before sending the "off" pulse.  This is useful to ensure that the PC has time to
  digest each pulse as a distinct event, by providing enough time between the two
  events that Windows realizes they're separate.

buttons[].type="toggle"
  This sets the button as a "toggle" button.  Each press of the underlying physical
  button flips the action between activated and deactivated.  The action remains
  activated or deactivated until the next press.  This is sort of the mirror image
  of the "pulse" button: it lets you take a physical input that's just a momentary
  pushbutton, and make it appear to the PC as though it's an On/Off switch.

buttons[].type="shift"
  This sets the button as a "shift" button, which makes it act like a modifier
  for the other buttons, akin to the SHIFT, ALT, CTRL keys on a PC keyboard.
  Whenever you press and hold a "shift" button, Pinscape turns on the "shift bits"
  defined for the button in its "shiftBits" property, adding them into the
  current "global shift bits" that affect all keys.  This continues as long as 
  you keep pressing the button, just like a CTRL key.  When you press another
  button, the other button looks at its own shift bits to see if they match 
  the current global shift bits, and it only executes its action if they do match.
  Each button also has a "shift mask", which defines which shift bits it pays
  attention to.  This lets you specify individually for each button whether or
  not it's affected by the shift modifiers.

  A shift button can act not only as a modifier, but also as an ordinary button
  in its own right, with its own action that's carried out when you press the
  button.  There are two variations on this.  The first is what we call a
  SHIFT-AND button.  This is the simpler of the two: when you press a SHIFT-AND
  button, it carries out its action just like any other button would, and it
  also activates its shift bits in the global shift state.  The other type is
  the SHIFT-OR button, which has a subtler way of working.  When you press
  a SHIFT-OR button, it adds its shift bits into the global shift state, but
  it doesn't carry out its action right away.  Instead, it bides it time,
  waiting to see if you're going to press any other buttons that are affected
  by its shift bits.  If you release the SHIFT-OR button without having pressed
  any other buttons while it was being held down, the SHIFT-OR button takes it
  that you were pressing the SHIFT-OR button for its own action rather than for
  its modifier function, and carries out its action for a programmed time,
  just like a "pulse" button would.  If you do press another button while the
  SHIFT-OR button is being held, the SHIFT-OR button considers its work done,
  assuming that you pressed it only for its modifier capability, so it doesn't
  execute its action when released.  To determine whether a shift button is a 
  SHIFT-AND button or a SHIFT-OR button, you simply look at the "tPulse"
  property: if present, it's a SHIFT-OR button, and if not, it's a SHIFT-AND
  button.

buttons[].type="shift".tPulse number optional
  This sets the pulse time, in milliseconds, for executing a SHIFT-OR button's
  action when the button is released after no other buttons were pressed.
  The very presence of this property (when type is "shift") makes the 
  button a SHIFT-OR button.  In the absence of this property, a shift button
  is a SHIFT-AND button that executes its action when it's pressed, whether
  or not you press any other buttons at the same time.

openPinballDevice object optional
  TOC: USB > Open Pinball Device
  TITLE: Open Pinball Device
  EXAMPLE:
  {
      openPinballDevice: {
          enable: true,
      },
  }

  Configures Open Pinball Device input to the PC.  Open Pinball Device is
  a proposed open-source standard for a custom HID device type specifically
  designed for pinball I/O controllers (such as Pinscape Pico) to use as a
  way to send accelerometer, plunger, and button input to the PC.  Pinball
  simulator programs such as Visual Pinball can use this interface as an
  alternative to the traditional joystick/gamepad mappings.  To enable the
  interface, simply set <b>OpenPinballDevice.enable</b> property to <b>true</b>.

  The details of the new interface are available in a published 
  <a href="http://mjrnet.org/pinscape/OpenPinballDevice/OpenPinballDeviceHID.htm">specification</a>,
  in the hope that other I/O controller devices and other pinball programs
  will also adopt it.  The goal is to provide a complete functional replacement
  for the traditional joystick/gamepad method of sending input to the simulators.
  One benefit is that the traditional joystick method occasionally causes conflicts
  with non-pinball video game software that expects HID joysticks to be literal
  joysticks; those conflicts can be eliminated by switching to an explicitly
  pinball-specific interface, since other video games won't try to access it.
  Another benefit is that a purpose-built interface will allow for easier
  configuration in the simulators, with less manual setup required.

  Newer versions of Visual Pinball have support for the Open Pinball Device
  interface.  To enable support in VP, use the Keys dialog to set each "axis"
  entry for the Nudge and Plunger settings to "Open Pin Dev".  That will select
  the corresponding Open Pinball Device axis.  While you're at it, you should
  also check the box "Nudge Input is Velocity", which uses the velocity-based
  nudge input that Pinscape Pico provides.  Velocity-based nudging should
  provide more natural nudge reactions in the simulator.

  The Open Pinball Device interface includes nudge and plunger readings.  By
  default, these are mapped to your accelerometer and plunger sensors in the
  obvious way, so you don't have to specify any extra properties to get the
  standard mappings.  However, you can override each axis individually with
  the axis properties: axNudge, ayNudge, etc.  If you want to disable one of
  the axes, set it to "null", which sets up the axis so that it reports a
  constant 0 reading to the PC.  This is especially useful if you have two
  or more Pinscape Pico units in your system, and both of them are equipped
  with accelerometers, since it lets you disable input to the PC from one of 
  the accelerometers.  The PC expects to see only one accelerometer and one
  plunger sensor reporting across the whole system, since it makes no sense
  to have multiple sensor inputs at once.  It's therefore useful to be able
  to disable sensor reporting selectively, so that you can designate one
  official accelerometer and one official plunger, and tell all of the other
  devices to keep quiet.

openPinballDevice.enable bool optional
  Set this to <b>true</b> to enable the Open Pinball Device interface on this
  Pinscape Pico unit.

openPinballDevice.axNudge string optional
  The logical axis source for the nudge acceleration X axis (left/right), using the same syntax as the <a href="#gamepad.x">gamepad axis</a> properties.
  The default value if this isn't specified is "nudge.x".

openPinballDevice.ayNudge string optional
  The logical axis source for the nudge acceleration Y axis (front/back), using the same syntax as the <a href="#gamepad.x">gamepad axis</a> properties.
  The default value if this isn't specified is "nudge.y".

openPinballDevice.vxNudge string optional
  The logical axis source for the nudge velocity X axis (left/right), using the same syntax as the <a href="#gamepad.x">gamepad axis</a> properties.
  The default value if this isn't specified is "nudge.vx".

openPinballDevice.vyNudge string optional
  The logical axis source for the nudge velocity Y axis (front/back), using the same syntax as the <a href="#gamepad.x">gamepad axis</a> properties.
  The default value if this isn't specified is "nudge.vy".

openPinballDevice.plungerPos string optional
  The logical axis source for the plunger position axis, using the same syntax as the <a href="#gamepad.x">gamepad axis</a> properties.
  The default value if this isn't specified is "plunger.z0".

openPinballDevice.plungerSpeed string optional
  The logical axis source for the plunger speed axis, using the same syntax as the <a href="#gamepad.x">gamepad axis</a> properties.
  The default value if this isn't specified is "plunger.speed".

gamepad object optional
  TOC: USB > Gamepad
  TITLE: USB Gamepad
  EXAMPLE:
  {
     gamepad: {
         enable: true,
         x: "nudge.x",
         y: "nudge.y",
         z: "plunger.z",
     },
  }

  Configures a virtual gamepad input to the PC.  Pinscape can optionally
  present itself to the PC as a simulated USB gamepad, with six analog joystick axes 
  (X, Y, Z, rotational RX, RY, RZ), two analog sliders, and 32 buttons.  
  Windows has good built-in support for USB gamepads, and most of the major
  pinball simulators can accept input via gamepads, so this makes an excellent
  way to map physical inputs on the Pico to game control functions in your pinball
  games.

  Pinscape only sets up the USB gamepad if you tell it to via this object.  (Gamepads
  can sometimes create compatibility problems for <i>other</i> gaming software you're 
  using, other than pinball simulators, which is why Pinscape makes this feature optional.)
  The gamepad can be combined with any of the other virtual USB devices (keyboard, XBox 
  controller).  Pinscape can emulate all of these devices at once.

  The mappings for joystick axes and sliders are specified as part
  of the <tt>gamepad</tt> property.  There are some common conventions for
  how the axes are mapped for the pinball simulators: the accelerometer nudge
  input is usually mapped to joystick X and Y, and the plunger is usually mapped
  to joystick Z.  But these mappings are only conventions, and most of the simulators
  are flexible about remapping them arbitrarily, so Pinscape doesn't impose any
  standard mappings.  It allows you to map any of the axis sources to any of the
  nominal joystick axes and sliders.

  Gamepad buttons <b>aren't</b> defined via the <tt>gamepad</tt> property.
  Instead, those mappings are handled in the <a href="#buttons"><tt>buttons</tt></a>
  section, where you specify the input ports where the physical buttons are
  connected, and what actions they perform when pressed.  One of the actions 
  you can assign there is to generate a joystick button press.

gamepad.enable bool optional
  Set this to true to enable the virtual USB gamepad, false to omit it from
  the USB setup.

gamepad.x string{table} optional
  Sets the data source for the gamepad's X axis.  This is optional; if you omit
  it, the axis will still be present in the USB virtual gamepad you see on the
  PC, but it'll just sit stationary at the center position all the time.  The
  axis data source is specified as a string, naming the underlying physical
  control to use as the axis position.
  <table>
    <tr><th>Axis name</th><th>Description</th></tr>
    <tr><td>"abs(<i>source</t>)"</td><td>Takes another source, such as "nudge.x", and takes the absolute value of each reading</td></tr>
    <tr><td>"ads1115[<i>n</i>]"</td><td>If an <a href="#ads1115">ADS1115</a> ADC chip is configured, reports the reading from the <i>n</i>th logical channel, numbered from 0</td></tr>
    <tr><td>"ads1115_<i>m</i>[<i>n</i>]"</td><td>If multiple <a href="#ads1115">ADS1115</a> ADC chips are configured, reports the reading from the <i>n</i>th logical channel of the <i>m</i>th chip, numbered from 0; for example, "ads1115_1[0]" selects the first channel of the second chip</td></tr>
    <tr><td>"gpio(<i>number</i>, <i>pull-mode</i>)"</td><td>Reads from the specified GPIO pin in digital (ON/OFF) mode, with a LOW reading (0V) reported as -32768, and HIGH (3.3V) reported as 32767; the optional <i>pull-mode</i> can be <tt>pull-up</tt> or <tt>pull-down</tt> to configure the internal pull-up/down resistor on the pin</td></tr>
    <tr><td>"lis3dh.temperature"</td><td>If an LIS3DH accelerometer is configured, reports the reading from its temperature sensor</td></tr>
    <tr><td>"lis3dh.x"</td><td>If an LIS3DH accelerometer is configured, reports the raw reading from its X axis</td></tr>
    <tr><td>"lis3dh.y"</td><td>If an LIS3DH accelerometer is configured, reports the raw reading from its Y axis</td></tr>
    <tr><td>"lis3dh.z"</td><td>If an LIS3DH accelerometer is configured, reports the raw reading from its Z axis</td></tr>
    <tr><td>"lis3dsh.temperature"</td><td>If an LIS3DSH accelerometer is configured, reports the reading from its temperature sensor</td></tr>
    <tr><td>"lis3dsh.x"</td><td>If an LIS3DSH accelerometer is configured, reports the raw reading from its X axis</td></tr>
    <tr><td>"lis3dsh.y"</td><td>If an LIS3DSH accelerometer is configured, reports the raw reading from its Y axis</td></tr>
    <tr><td>"lis3dsh.z"</td><td>If an LIS3DSH accelerometer is configured, reports the raw reading from its Z axis</td></tr>
    <tr><td>"mc3416.x"</td><td>If an MC3416 accelerometer is configured, reports the raw reading from its X axis</td></tr>
    <tr><td>"mc3416.y"</td><td>If an MC3416 accelerometer is configured, reports the raw reading from its Y axis</td></tr>
    <tr><td>"mc3416.z"</td><td>If an MC3416 accelerometer is configured, reports the raw reading from its Z axis</td></tr>
    <tr><td>"mxc6655xa.temperature"</td><td>If an MXC6655XA accelerometer is configured, reports the reading from temperature sensor</td></tr>
    <tr><td>"mxc6655xa.x"</td><td>If an MXC6655XA accelerometer is configured, reports the raw reading from its X axis</td></tr>
    <tr><td>"mxc6655xa.y"</td><td>If an MXC6655XA accelerometer is configured, reports the raw reading from its X axis</td></tr>
    <tr><td>"mxc6655xa.z"</td><td>If an MXC6655XA accelerometer is configured, reports the raw reading from its X axis</td></tr>
    <tr><td>"negate(<i>source</i>)"</td><td>Takes another source, such as "nudge.x", and reports the negative of the original value</td></tr>
    <tr><td>"nudge.vx"</td><td>Nudge X velocity, from the processed nudge information as configured in the "nudge" configuration section</td></tr>
    <tr><td>"nudge.vy"</td><td>Nudge Y velocity, from the processed nudge information as configured in the "nudge" configuration section</td></tr>
    <tr><td>"nudge.vz"</td><td>Nudge Z velocity, from the processed nudge information as configured in the "nudge" configuration section</td></tr>
    <tr><td>"nudge.x"</td><td>Nudge X acceleration, from the processed nudge information as configured in the "nudge" configuration section</td></tr>
    <tr><td>"nudge.y"</td><td>Nudge Y acceleration, from the processed nudge information as configured in the "nudge" configuration section</td></tr>
    <tr><td>"nudge.z"</td><td>Nudge Z acceleration, from the processed nudge information as configured in the "nudge" configuration section</td></tr>
    <tr><td>"null"</td><td>No data source; just sits at 0 (the center position)</td></tr>
    <tr><td>"offset(<i>source, amount</i>)"</td><td>Takes another source, such as "nudge.x", and adds a fixed offset to each reading</td></tr>
    <tr><td>"pico_adc"</td><td>If the Pico ADC is configured (via "pico_adc"), reports the input reading from its first configured channel</td></tr>
    <tr><td>"pico_adc[0]"</td><td>Same as pico_adc</td></tr>
    <tr><td>"pico_adc[1]"</td><td>Reports the second Pico ADC channel, if two or more channels are configured</td></tr>
    <tr><td>"pico_adc[2]"</td><td>Reports the third Pico ADC channel, if three or more channels are configured</td></tr>
    <tr><td>"pico_adc[3]"</td><td>Reports the fourth Pico ADC channel, if four or more channels are configured</td></tr>
    <tr><td>"plunger.sensor"</td><td>The raw plunger sensor reading, bypassing calibration and other processing</td></tr>
    <tr><td>"plunger.speed"</td><td>The current plunger speed reading</td></tr>
    <tr><td>"plunger.z"</td><td>The standard processed plunger position, taking into account calibration and firing event detection</td></tr>
    <tr><td>"plunger.z0"</td><td>The calibrated plunger position, without any firing event detection</td></tr>
    <tr><td>"scale(<i>source, amount</i>)"</td><td>Takes another source, such as "nudge.x", and scales it by a constant factor</td></tr>
    <tr><td>"sine(<i>period, offset</i>)"</td><td>A synthesized sine wave, with the given period in milliseconds and starting offset in millseconds</td></tr>
  </table>

gamepad.y string optional
  Sets the data source for the gamepad's Y axis, using the same notation as gamepad.x.

gamepad.z string optional
  Sets the data source for the gamepad's Z axis, using the same notation as gamepad.x.

gamepad.rx string optional
  Sets the data source for the gamepad's RX (rotational X) axis, using the same notation as gamepad.x.

gamepad.ry string optional
  Sets the data source for the gamepad's RY (rotational Y) axis, using the same notation as gamepad.x.

gamepad.rz string optional
  Sets the data source for the gamepad's RZ (rotational Z) axis, using the same notation as gamepad.x.

gamepad.slider1 string optional
  Sets the data source for the gamepad's Slider #1 axis, using the same notation as gamepad.x.

gamepad.slider2 string optional
  Sets the data source for the gamepad's Slider #2 axis, using the same notation as gamepad.x.

xInput object optional
  TOC: USB > XBox Controller
  TITLE: XBox Controller Emulation
  EXAMPLE:
  {
     // typical configuration for PinballFX games
     xInput: {
         enable: true,
         xLeft: "nudge.x",              // PinballFX nudge input is on left joystick X (left/right)...
         yLeft: "nudge.y",              //  ...and Y (front/back)
         xRight: "negate(plunger.z)",   // PinballFX plunger is on right X, using reversed direction from Pinscape convention
     },
  }

  Configures a virtual XBox controller input to the PC.  This makes the Pico emulate
  an XBox 360 controller, including all of the standard XBox controller buttons, joysticks,
  and triggers.  You select which physical buttons trigger which emulated XBox controller
  buttons, and which analog inputs on the Pico sides map to which joystick axes on the 
  virtual XBox controller.

  The XBox controller emulation is optional.  Pinscape only enables it if you explicitly
  tell it to, which you do by including the <tt>xInput</tt> section in your JSON configuration.
  The XBox controller emulation can be combined with any of the other USB devices, including
  the USB keyboard and USB gamepad emulations.

  <b>PinballFX users:</b>
  In a virtual pinball context, the XBox controller emulation is especially useful for
  the PinballFX series of games, which have support for XBox input but not for regular
  gamepads.  PinballFX accepts nudge input on the XBox left joystick axes:  <tt>xLeft</tt>
  for left/right nudging, <tt>yLeft</tt> for front/back nudging.  PinballFX uses the right
  joystick X axis (<tt>xRight</tt>) for plunger input, but it uses the opposite direction
  from Pinscape (which follows the Visual Pinball convention).  You can accomplish the
  direction reversal by mapping <tt>xRight</tt> to <tt>"negate(plunger.z)"</tt>.

  <b>Device driver setup:</b>  When you configure a virtual XBox controller input, you
  <b>MUST</b> go through a one-time manual device driver installation procedure in Windows:
  <ul>
    <li>First, finish configuring the Pico with the xInput section enabled
    <li>Save the new configuration to the Pico so that it reboots with the new settings in effect
    <li>Open Device Manager, and find the PinscapePicoXInput device
    <li>Double-click the device in Device Manager to open its Properties page
    <li>Select the <b>Driver</b> tab and click <b>Update Driver</b>
    <li>Click <b>Browse my computer for drivers</b>
    <li>Click <b>Let me pick from a list of available drivers on my computer</b>
    <li>Find the <b>XBox 360 Peripherals</b> section, and select <b>XBox 360 Controller for Windows</b>
    <li>Click through the warning (this appears because Windows can tell from the USB IDs that this isn't really an XBox controller)
  </ul>
  This manual procedure is required because Windows doesn't automatically recognize
  a Pico as an XBox controller unit, even when you configure the Pico to perform the
  emulation.  Windows only recognizes an XBox controller automatically when it
  uses the official Microsoft USB VID/PID codes, which Pinscape doesn't do, because it
  could create compatibility problems for other software if the Pico claimed to be
  an XBox device at the USB level.  Fortunately, you can "force" Windows to recognize
  the Pico as an XInput source using the manual driver setup procedure above

  You should only have to complete this manual procedure once, during initial setup,
  although you might have to repeat it if you ever change the Pinscape configuration
  in such a way that you add or remove USB interfaces - for example, if you enable or
  disable the USB keyboard or gamepad emulations.  If you're not sure whether you
  have to re-install the device drivers, just check Device Manager for a PinscapePicoXInput
  device flagged with a warning or error icon.  If you see an error icon, repeat the
  procedure above, and that should clear it up again.

xInput.enable bool optional
  Enable the virtual XBox controller interface.  False by default.

xInput.xLeft string optional
  Sets the input data source for the virtual XBox controller's left joystick X axis.
  This uses the same notation as gamepad.x.

xInput.yLeft string optional
  Sets the input data source for the virtual XBox controller's left joystick Y axis.
  This uses the same notation as gamepad.x.

xInput.xRight string optional
  Sets the input data source for the virtual XBox controller's right joystick X axis.
  This uses the same notation as gamepad.x.

xInput.yRight string optional
  Sets the input data source for the virtual XBox controller's right joystick Y axis.
  This uses the same notation as gamepad.x.

xInput.leftTrigger string optional
  Sets the input data source for the virtual XBox controller's left trigger axis.
  This uses the same notation as gamepad.x.

xInput.rightTrigger string optional
  Sets the input data source for the virtual XBox controller's right trigger axis.
  This uses the same notation as gamepad.x.


i2c0 object optional
  TOC: I2C > I2C0 (Pico I2C unit 0)
  TITLE: I2C Setup (I2C0)
  EXAMPLE:
  {
     i2c0: {
         sda: 8,
         scl: 13,
         speed: 400000
     },
  }

  Configures the Pico's I2C0 bus controller.

  I2C is an industry-standard bus interface that allows multiple external peripherals to
  be connected to the Pico through just two GPIO ports ("SDL" and "SCL", for the data and
  clock signals, respectively).  Being able to connect multiple peripherals through just
  two ports is extremely helpful with the Pico given its relatively small number of GPIO
  pins.  The Pico has two I2C units, which lets you set up two separate I2C buses that
  can operate concurrently (which can be useful if you have some peripherals that hog
  the bus with large and/or frequent transfers, since only one peripheral on each bus
  can be transferring data at any given time).

  The "i2c0" JSON object sets up the configuration for the first of the two I2C units.
  The two units are identical, except that each one connects to a
  different subset of the GPIO pins, so the choice of which unit to use boils down to
  which pins you plan to connect to.  If you're using pins that are only wired internally
  to I2C0, you have to use the I2C0 unit, and likewise for pins connecting to I2C1.
  The main thing you have to configure for each I2C unit is the GPIO pins it's using:
  one for the "SDA" function, one for the "SCL" function.  In the physical wiring,
  you connect the designated Pico SDA pin to the SDA pins for each of the peripherals
  that you want to attach to the bus, and likewise for the SCL pins.

i2c0.sda number{0 4 8 12 16 20} required
  Sets the GPIO port number for the SDA function for this I2C unit.  The GPIO port
  selected must be one of the I2C0 SDA capable pins: 0, 4, 8, 12, 16, or 20.

i2c0.scl number{1 5 9 13 17 21} required
  Sets the GPIO port number for the SCL function for this I2C unit.  The GPIO port
  selected must be one of the I2C0 SCL capable pins: 1, 5, 9, 13, 17, or 21.

i2c0.speed number optional
  Sets the bit rate for the I2C bus; the default is 400000, which is compatible
  with all of the devices that Pinscape currently supports.  The Pico's I2C units
  support speeds from 0 to 1000000 bits per second, but speeds above 400000
  aren't as widely supported by peripheral devices.

i2c0.pullup bool optional
  Controls the internal pull-up resistors on the SDA and SCL GPIO ports.  Set
  to <tt>true</tt> to enable the internal pull-ups, <tt>false</tt> to disable them.
  The default if this isn't specified is <tt>true</tt>.

  The I2C bus design requires pull-up resistors on the SDA and SCL lines, to the
  bus logic level (3.3V for the Pico).  One easy way to satisfy this requirement
  is to enable the Pico's internal GPIO port pull-up resistors on the SDA and SCL
  ports.  However, this isn't considered good practice, because the Pico's
  internal pull-ups are too weak.  Typical I2C pull-up resistors should be in
  the neighborhood of 4K to 10K ohms (the exact value depends upon how many
  chips are sharing the bus), whereas the Pico's internal pull-ups are
  around 50K.  The difference can affect signal quality on the bus, so it's
  better to use external pull-ups where you can choose the appropriate value
  according to the bus configuration.  If your hardware design does include
  its own pull-ups, it's best to disable the Pico's internal ones, so that
  they're not added in parallel to the values you specifically chose.

  Another scenario where it might be important to disable the internal pull-ups
  is where the chips on your I2C bus have a separate power supply from the
  Pico's 3.3V supply.  The reference Pinscape Pico Expansion Boards use such
  a design, to allow the Pico to perform a hard reset on the peripheral chips
  by power-cycling them under software control.  It might be harmful to some
  peripherals to feed them power via the I2C bus lines while their main power
  input is disabled, so in this setup it's best to provide power to the I2C
  pullups through the peripheral power supply rather than through the Pico's
  main 3.3V power, which is what the internal pull-ups are connected to.

i2c0.enable string|bool optional
  Sets the operating mode for the bus:
  <ul>
    <li><b>true</b> - enable the bus unconditionally; this is the default if <tt>enable</tt> is omitted
    <li><b>false</b> - disable the bus; equivalent to omitting the i2c0 definition entirely
    <li><b>"on-demand"</b> - enable the bus only if one or more devices are configured on it
  </ul>
  The "on-demand" setting lets you define the bus's GPIO assignments in the JSON
  configuration file without actually tying up the GPIO pins if there aren't any
  devices on the bus.  This is mostly to make it easier to write "template"
  configuration files that adapt automatically to different configurations without
  the need to manually edit dependent elements.

i2c1 object optional
  TOC: I2C > I2C1 (Pico I2C unit 1)
  TITLE: I2C Setup (I2C1)
  EXAMPLE:
  {
     i2c0: {
         sda: 10,
         scl: 27,
         speed: 100000
     },
  }

  Configures the Pico's I2C1 bus controller (the second of the Pico's two I2C controllers).
  The contents are the same as for the "i2c0" object.  The I2C1 unit is only connected
  internally within the Pico to a subset of the GPIO ports, so you can only configure
  I2C1 with that limited set of ports.

i2c1.sda number{2 6 10 14 18 26} required
  Sets the GPIO port number for the SDA function for this I2C unit.  The GPIO port
  selected must be one of the I2C1 SDA capable pins: 2, 6, 10, 14, 18, or 26.

i2c1.scl number{3 7 11 15 19 27} required
  Sets the GPIO port number for the SCL function for this I2C unit.  The GPIO port
  selected must be one of the I2C1 SCL capable pins: 3, 7, 11, 15, 19, or 27.

i2c1.speed number optional
  Sets the bit rate for the I2C bus; the default is 400000, which is compatible
  with all of the devices that Pinscape currently supports.  The Pico's I2C units
  support speeds from 0 to 1000000 bits per second, but speeds above 400000
  aren't as widely supported by peripheral devices.

i2c1.enable string|bool optional
  Sets the operating mode for the bus:
  <ul>
    <li><b>true</b> - enable the bus unconditionally; this is the default if <tt>enable</tt> is omitted
    <li><b>false</b> - disable the bus; equivalent to omitting the i2c1 definition entirely
    <li><b>"on-demand"</b> - enable the bus only if one or more devices are configured on it
  </ul>
  The "on-demand" setting lets you define the bus's GPIO assignments in the JSON
  configuration file without actually tying up the GPIO pins if there aren't any
  devices on the bus.  This is mostly to make it easier to write "template"
  configuration files that adapt automatically to different configurations without
  the need to manually edit dependent elements.

i2c1.pullup bool optional
  Controls the internal pull-up resistors on the SDA and SCL GPIO ports.  Set
  to <tt>true</tt> to enable the internal pull-ups, <tt>false</tt> to disable them.
  The default if this isn't specified is <tt>true</tt>.

  The I2C bus design requires pull-up resistors on the SDA and SCL lines, to the
  bus logic level (3.3V for the Pico).  One easy way to satisfy this requirement
  is to enable the Pico's internal GPIO port pull-up resistors on the SDA and SCL
  ports.  However, this isn't considered good practice, because the Pico's
  internal pull-ups are too weak.  Typical I2C pull-up resistors should be in
  the neighborhood of 4K to 10K ohms (the exact value depends upon how many
  chips are sharing the bus), whereas the Pico's internal pull-ups are
  around 50K.  The difference can affect signal quality on the bus, so it's
  better to use external pull-ups where you can choose the appropriate value
  according to the bus configuration.  If your hardware design does include
  its own pull-ups, it's best to disable the Pico's internal ones, so that
  they're not added in parallel to the values you specifically chose.

  Another scenario where it might be important to disable the internal pull-ups
  is where the chips on your I2C bus have a separate power supply from the
  Pico's 3.3V supply.  The reference Pinscape Pico Expansion Boards use such
  a design, to allow the Pico to perform a hard reset on the peripheral chips
  by power-cycling them under software control.  It might be harmful to some
  peripherals to feed them power via the I2C bus lines while their main power
  input is disabled, so in this setup it's best to provide power to the I2C
  pullups through the peripheral power supply rather than through the Pico's
  main 3.3V power, which is what the internal pull-ups are connected to.

keyboard object optional
  TOC: USB > Keyboard
  TITLE: USB Keyboard Setup
  EXAMPLE:
  {
     keyboard: {
         enable: true,
     },
  }

  Configures virtual USB keyboard input to the PC.  Pinscape can optionally
  present itself to the PC as a USB keyboard, allowing you to set up buttons
  to send key presses to the PC as though you were pressing the keys on a
  physical keyboard.  Windows handles mulitple keyboards seamlessly, so 
  enabling the Pinscape virtual keyboard won't affect your actual keyboard.
  You can combine the virtual keyboard with any of the other virtual USB
  devices (gamepad, XBox controller) - Pinscape can emulate all of these
  device types at once.

  Note that you don't specify any key mappings as part of the 'keyboard'
  section in the JSON file.  Instead, you define key presses in the parts
  of the JSON file related to handling input that triggers key presses,
  particular the <a href="#buttons">buttons</a> section.

keyboard.enable bool optional
  Set this to true to enable the keyboard emulation.  Pinscape won't create
  its virtual keyboard unless you explicitly tell it to by setting this
  to true.

logging object optional
  TOC: Message Logging
  TITLE: Message Logging
  EXAMPLE:
  {
     logging: {
        bufSize: 8192,
        filter: "warning error info config",
        timestampe: true,
        typeCodes: true,
        colors: true,
     },
  }

  Customizes the message logging options.  As the Pinscape firmware runs,
  it generates a series of human-readable messages that describe important
  events, especially things related to the initial setup after a reboot,
  when the software is going through the JSON configuration file and
  initializing all of its internal modules and external hardware peripherals.
  Log messages include confirmations when setup tasks succeed, and error
  messages when tasks fail, all intended to help you troubleshoot any
  problems you're noticing with the system.   The "logging" object lets
  you customize details about the log message store.

  The log messages are kept in
  RAM on the Pico, but you can view them at any time using the Pinscape
  Config Tool, or by connecting a terminal window to one of the Pico's
  serial ports - its USB virtual COM port, or its physical UART port.

feedbackController object optional
  TOC: USB > Feedback Controller
  TITLE: Feedback Controller USB Interface
  EXAMPLE:
  {
     feedbackController: {
         enable: true,
     },
  }

  Configures Pinscape Pico's custom USB HID protocol interface, which
  host PC programs can use to send commands to the Pico to activate
  and control feedback device output ports.  This is the interface
  that DOF uses to activate feedback effects on the Pico, and the
  protocol is documented, so it's available to any other programs
  that wish to use it.

  The Feedback Controller interface is enabled by default.  The only
  scenario where you should disable it is for strict LedWiz emulation.
  A genuine LedWiz has only one HID interface, which accepts commands
  using the proprietary LedWiz protocol.  If you want to make a
  Pinscape Pico unit fully emulate an LedWiz at the USB level, it's
  necessary to disable all of Pinscape's other HID interfaces, including
  this one, as well as the keyboard, gamepad, XInput, and Open Pinball
  Device interfaces.  See the <a href="#ledWizProtocol"><tt>ledWizProtocol</tt></a>
  object for more details on setting up LedWiz emulation.

feedbackController.enable bool optional
  Enables or disables the interface.  The interface is enabled by
  default.  The only common reason for disabling it is for <a href="#ledWizProtocol">strict LedWiz emulation</a>.

feedbackController.macCompatibleUsage bool optional
  Selects the HID usage codes reported by the device for the Feedback Controller
  interface.  If this property is false (the default), the <b>original</b> codes
  are used (Usage Page 6, Generic Device, usage 0, undefined/vendor-defined).
  Setting this to true selects the <b>alternative</b> usage codes
  (Usage Page 0xFF06, Vendor-Defined, usage 1).

  The alternative HID usage codes are primarily for MacOS, where the newer
  versions of the operating system block application access to HID devices
  in any of the pre-defined usage code ranges.  This prevents DOF and other
  programs from accessing the Feedback Controller interface without privilege
  elevation (via "sudo"), which creates separate problems of its own.  To
  work around this, the Feedback Controller must use a Usage Code in the
  special "Vendor-Defined" range, in Usage Pages 0xFF00 through 0xFFFF.
  Setting this property to true selects a usage code in this range.

  Note that application software on the client side uses the usage codes
  to identify the device, so setting this property to true will hide the
  device from clients that are programmed to look for the original usage
  codes.  Currently, all of the Windows client programs (including DOF and
  the Pinscape Config Tool) only recognize the original codes, so you
  should use the default settings with Windows hosts for now.  Future
  versions of the clients will recognize both codes, so eventually it should
  be possible to use either setting with any client, but for the moment
  you should only set this property to true for MacOS hosts, and you
  must make sure that you're using an updated versions of DOF and any
  other software that accesses the Feedback Controller interface.
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
