mjrgh/PinscapePico/Firmware/Devices/PWM/PWMWorker.cpp

// Pinscape Pico firmware - PWMWorker device interface
// Copyright 2024, 2025 Michael J Roberts / BSD-3-Clause license / NO WARRANTY
//
// Defines the Pinscape Pico interface to the PWMWorker device.  A
// PWMWorker is a Pico running our special PWMWorker firmware, which
// turns the Pico into an I2C slave device that exposes an interface
// similar to a dedicated PWM controller chip like a TLC59116 or
// PCA9685.  A Pico running PWMWorker can act as a substitute for PWM
// chips of that sort, providing 24 channels of PWM outputs through GPIO
// pins (the other two GPIOs provide the I2C connection to the host Pico
// running Pinscape).

// standard library headers
#include <stdio.h>
#include <stdint.h>
#include <string.h>
#include <unordered_set>
#include <vector>
#include <memory>

// Pico SDK headers
#include <pico/stdlib.h>
#include <hardware/i2c.h>
#include <hardware/watchdog.h>

// local project headers
#include "Utils.h"
#include "Pinscape.h"
#include "I2C.h"
#include "Logger.h"
#include "Config.h"
#include "JSON.h"
#include "Outputs.h"
#include "../USBProtocol/VendorIfcProtocol.h"
#include "CommandConsole.h"
#include "PWMWorker.h"

// device instances
std::vector<std::unique_ptr<PWMWorker>> PWMWorker::units;

// get a unit by configuration index
PWMWorker *PWMWorker::GetUnit(int n)
{
    return n >= 0 && n < static_cast<int>(units.size()) ? units[n].get() : nullptr;
}

// Configure from JSON data
//
// workerPico: [
//   // Pico #0
//   {
//     i2c: <number>,          // I2C bus number (0 or 1)
//     addr: <number>,         // I2C bus address for this chip, 7-bit notation
//     pwmFreq: <number>,      // PWM frequency for the ports on this chip
//   },
//   // Pico #1, ...
// ]
//
void PWMWorker::Configure(JSONParser &json)
{
    // set the native unit array size to match the JSON array
    auto *cfg = json.Get("workerPico");
    if (cfg->IsObject() || cfg->IsArray())
    {
        // make room
        units.resize(cfg->Length(1));
    
        // parse each entry in the array (or just the single object, if it's not an array)
        cfg->ForEach([](int index, const JSONParser::Value *value)
        {
            // get and validate the I2C bus number
            char facility[30];
            snprintf(facility, _countof(facility), "workerPico[%d]", index);
            int bus = value->Get("i2c")->Int(-1);
            if (!I2C::ValidateBusConfig(facility, bus))
                return;

            // get and validate the I2C address
            uint8_t addr = value->Get("addr")->UInt8(0);
            if (addr == 0)
            {
                Log(LOG_ERROR, "workerPico[%d]: invalid/undefined I2C address\n", index);
                return;
            }
            if (addr < 8 || addr >= 0x7C)
            {
                Log(LOG_ERROR, "workerPico[%d]: invalid I2C address 0x%02x (0x00-0x07 and 0x7C-0x7F are reserved)\n", index, addr);
                return;
            }

            // get and validate the PWM frequency
            int pwmFreq = value->Get("pwmFreq")->Int(20000);
            if (pwmFreq < 8 || pwmFreq > 65535)
            {
                Log(LOG_ERROR, "workerPico[%d]: invalid PWM frequency; must be 8-65535\n", index, pwmFreq);
                return;
            }

            // create the instance and enroll it in the unit list at the same index
            // as the JSON source data  
            auto *unit = new PWMWorker(index, i2c_get_instance(bus), addr, pwmFreq);
            units[index].reset(unit);

            // add it to the I2C bus manager for the selected bus
            I2C::GetInstance(bus, false)->Add(unit);

            // set the initialization timeout, if specified, converting from millisecond
            // units in the JSON to microsecond units internally
            unit->initTimeout = value->Get("initTimeout")->UInt32(20) * 1000UL;

            // success
            Log(LOG_CONFIG, "workerPico[%d] configured on I2C%d addr 0x%02x\n", index, bus, addr);
        }, true);
    }
    else if (!cfg->IsUndefined())
    {
        Log(LOG_ERROR, "Config: 'workerPico' key must be an object or array\n");
    }

    // Initialize all of the units
    int nConfigured = 0;
    for (auto &unit : units)
    {
        if (unit != nullptr)
        {
            unit->Init();
            ++nConfigured;
        }
    }

    // if any units are configured, add the console command
    if (nConfigured != 0)
    {
        struct PWMWorkerClass : CommandConsole::PWMChipClass
        {
            PWMWorkerClass()
            {
                name = "WorkerPico";
                nInstances = units.size();
                maxLevel = 255;
                selectOpt = "-u <number>\tselect unit number; default is 0\n--unit <num>\tsame as -u";
            }
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
